dmz006/brain-drain/hardware/review/erc-summary.md

# ERC summary

kicad-cli 9 `sch erc`.

## brain

* 0 ERC findings (0 errors)

## card

* 2 ERC findings (0 errors)
  * warning: lib_symbol_mismatch: Symbol '2N7002' doesn't match copy in library 'Transistor_FET' (Symbol Q3 [2N7002])
  * warning: lib_symbol_mismatch: Symbol '2N7002' doesn't match copy in library 'Transistor_FET' (Symbol Q4 [2N7002])
