dmz006/brain-drain/hardware/review/routing-stats.md

# Routing statistics

Generated by `hardware/tools/make_review_pack.py`.

## brain

* 167 footprints, 192 nets, 3422 track segments, 568 vias
* copper length by layer (mm): B.Cu 466, F.Cu 1244, In2.Cu 4567, In3.Cu 5079
* vias (diameter / drill): 0.3/0.15 x 53, 0.45/0.2 x 480, 0.6/0.3 x 35
* differential-pair copper by layer (mm): B.Cu 202, F.Cu 372, In2.Cu 2250, In3.Cu 1812

**Reference planes of the pairs (review item):** pairs on In2 have the solid GND plane In1 next to them. Pairs on In3 have In4 next to them, which is split into power islands. Sampled every 0.5 mm along the In3 pair copper:

| plane under the pair (In4) | samples |
|---|---|
| +3V3 | 1315 |
| 5V_SYS | 1189 |
| +12V | 761 |
| 5V_HDD | 670 |

* 38 island-to-island transitions inside single segments, on 19 pair nets (each is a return-path discontinuity; stitching capacitors or a re-assigned In4 are the fixes).
* 833 of 3935 In3 pair samples (21 %) have an In2 track within 0.3 mm in plan view: broadside coupling between the two adjacent inner signal layers.

* 44 differential pairs, end-to-end skew (across the series capacitors) max 0.00 mm, table in `routing/pairs.md`

## card

* 39 footprints, 37 nets, 676 track segments, 133 vias
* copper length by layer (mm): B.Cu 742, F.Cu 694
* vias (diameter / drill): 0.3/0.15 x 31, 0.45/0.2 x 81, 0.6/0.3 x 21
* differential-pair copper by layer (mm): B.Cu 352, F.Cu 272

* 8 differential pairs, end-to-end skew (across the series capacitors) max 0.09 mm, table in `bay-card/routing/pairs.md`
