dmz006/brain-drain/docs/DECISIONS.md

# Decisions log

Open items block layout or software structure. Closed items record what was
chosen and why, so nobody re-litigates them later.

## Open

| # | Decision | Options | Recommendation | Blocks |
|---|---|---|---|---|
| D5 | OLED | 0.96"/1.3" 4-pin I2C vs 2.42" SSD1309 | 0.96"/1.3" for v1 | enclosure |
| D8 (applied 2026-09-23, pipeline rerunning) | Small vias for the QFN supply pins | 0.3 mm via / 0.15 mm drill for the dog-bones on the ASM1153E and USB5744 pins (0.4 mm pitch), staggered in two rows; JLCPCB lists 0.15 mm holes as standard on 4-layer boards (check the day's price list); everything else stays at 0.45/0.2 | recommended next lever: the 35 bridge-rail links and most of the 53 plane pins are exactly these pins; cheap to try, one pipeline rerun (about 5 h) | routing |
| D7 | Finishing the board | **(b) chosen 2026-09-23** ("try b, size can increase some if it helps"): board v3 at 150 × 112 mm, 2.5 mm around every QFN, hubs under the CM5's USB 3 pins, M.2 front-right; pipeline rerun: 81 % -> 83 %, pairs 9 -> 21 routed. Alternatives kept: (a) a board designer finishes the rest in the KiCad GUI; (c) finer fab rules (0.1 / 0.1 mm, 0.3/0.15 vias), now narrowed to D8 | owner's call | routing |
| D9 (decided: C24) | Bay cards and an 8-port brain | (1) stay monolithic, 4 bays; (2) brain + eight identical bay cards on PCIe-x1-style card-edge slots along the rear (bridge, switch, LED and receptacle per card; all 4 downstream ports of each hub used); (3) bridge at the drive end over USB-C (rejected: needs USB PD per port); (4) hub+bridges mezzanine (no gain) | (2) if 8 ports matter: the hard routing leaves the brain, the card routes in minutes and is built 8 times; box grows to ~155 × 120 × 55 mm, brick to 150–180 W, 8 drives at once share two 5 Gb/s uplinks. Brief: `decisions/2026-09-23-bay-cards.md` | architecture |
| D6 | Option B: bridges move into the cables | board = CM5 + hubs + 4× USB-A + switched 12 V/5 V outputs, about 90 × 70 mm; commercial USB 3 to SATA cables | parked by the owner on 2026-09-23 as a later study; A (C21) is being built | nothing now |
| D8 | Build order | software-sim first / schematic first / enclosure first | software-sim first (ARCHITECTURE §8) | everything |

## Closed

| # | Decision | Chosen | Why | Date |
|---|---|---|---|---|
| C1 | Drive pigtail | Off-the-shelf 22-pin SATA M-F extension; board has backplane-style 22-pin receptacles | no custom cable, drive end is native | 2026-09-21 |
| C2 | Staggered spin-up | Mandatory, per-bay P-FET switches on 12 V and 5 V from GPIO | halves peak input current; also gives unfreeze/reset | 2026-09-21 |
| C3 | Two 5 V bucks | separate 5V_SYS and 5V_HDD, same TPS56637 | keep spin-up ripple off the CM5 rail | 2026-09-21 |
| C4 | RTC on board | PCF85063AT + CR2032 | certificates need timestamps off-network | 2026-09-21 |
| C5 | Default wipe policy | HDD: 1-pass zeros + full verify (Clear). SSD: Sanitize crypto-scramble then block-erase (Purge). Multi-pass only as explicit legacy modes | NIST 800-88 Rev. 2 | 2026-09-21 |
| C6 | Enclosure tool | OpenSCAD with params generated from KiCad | ubiquitous, easy to diff | 2026-09-21 |
| C7 (was D9) | Compute module | **CM5** | $10 over CM4 at equal RAM/eMMC; 2× native USB 3.0 so four HDDs run at native speed; PCIe Gen3 x1 left free; on-module RTC | 2026-09-22 |
| C8 (was D1, D4) | USB 3 topology | CM5 USB 3.0 port → VL817 hub → 2× ASM1153E, twice. No PCIe xHCI | ~400 MB/s per pair of bays, no firmware loading, uses the originally requested VL817 | 2026-09-22 |
| C9 (was D6) | Module size | CM5002016 (2 GB, 16 GB eMMC) for production; CM5002000 Lite via microSD for dev | service needs < 1 GB; eMMC can't fall out mid-job; same carrier serves both | 2026-09-22 |
| C10 | User interaction | No Start button. A drive is wiped as soon as it is detected (after a 5 s grace countdown); unplugging aborts; DIP is the only control | single-purpose appliance, keep it simple | 2026-09-22 |
| C11 | USB 3.0 hub | **Microchip USB5744**, one per CM5 USB 3.0 port | same 4-port 5 Gbit/s spec as VL817; fully public datasheet; smallest and cheapest; JLCPCB-assembled; +1 LDO for 1.2 V core | 2026-09-23 |
| C12 (was D3) | USB→SATA bridge | **ASMedia ASM1153E** | dmz's call: Linux track record (UASP+TRIM, no quirks) over the public-datasheet rule; datasheet from a mirror copy, kept locally in hardware/ref/datasheets (not committed) | 2026-09-23 |
| C13 (was D2) | 12 V input | **4-pin DIN Kycon KPJX-4S-S only**; barrel footprint dropped | barrels are 5 A rated, design peak is 7.4 A; DIN is 7.5 A/pin and what 12 V/10 A bricks ship with. Brick must be chosen before layout to match DIN pin assignment | 2026-09-23 |
| C14 (was D7) | Panel LEDs | **3 mm through-hole**, 6 off | cheapest, tolerant of enclosure error, bay LEDs blink with real disk activity | 2026-09-23 |
| C15 (was D10) | M.2 NVMe bay | **Populated in v1**: M.2 M-key on PCIe Gen3 x1, switched 3V3, enclosure access door | dmz's call: NVMe wipes from day one; accepts door + PCIe rescan software as v1 work | 2026-09-23 |
| C16 | Schematic workflow | **Generated**: `hardware/tools/design.py` is the source of truth; `gen_sch.py` regenerates the KiCad sheets and `gen_connections.py` the connection list on every change; placement is tidied in the GUI only once the netlist settles | ERC on every edit, repeated bay sheets cannot drift, connection list always in sync | 2026-09-23 |
| C17 | SATA bay receptacle | **Molex 47018-4001**, right-angle SMT 22-pin host receptacle | industry standard, precise sales drawing SD-47018-001, easy small-quantity sourcing | 2026-09-23 |
| C18 | M.2 socket | **TE 2199230-4**, 4.2 mm M-key | most common small-run M.2 socket, stocked at distributors and JLCPCB | 2026-09-23 |
| C19 | Board outline | **Option A: 180 × 110 mm**, all cables on the rear edge (DIN, RJ45, USB-C/UART, 4× SATA), CM5 centred, M.2 along the front with its door on a side wall | one enclosure wall with cutouts, single cable exit, M.2 door away from cables, fits a 220 mm print bed | 2026-09-23 |
| C20 | Licence | **Polyform Noncommercial 1.0.0** for hardware, software and enclosure | matches the owner's datawatch project; source-available, noncommercial | 2026-09-23 |
| C22 | Wireless instead of Ethernet | **Option A**: CM5 wireless variant, unit runs a Wi-Fi access point with an ephemeral 8-character key regenerated at every boot and shown on the OLED as text and as a Wi-Fi QR code; a phone page (stdlib HTTP) shows status, certificates (download one or all), the log, and lets the owner push a network to join (remembered, joined at boot) or reset. Wi-Fi reset / factory reset from the page (with the key), from DIP mode 110 at boot (110 + DIP 8 = factory), or `braindrain wifi-reset`. RJ45 magjack removed. CM5 antenna edge on the left board edge, 8 mm copper-free strip, no metal within 10 mm | standalone appliance; the owner asked for ESPHome-style ephemeral provisioning, liked the QR code, and wants certificates reachable from a phone | 2026-09-23 |
| C23 | No buzzer, passive cooling, lid opens for the M.2 | Buzzer, its FET and diode removed (GPIO18 free). Passive CM5 cooler by default, fan header kept. The M.2 socket sits flat on the board and the lid hinges open (rear hinge, front snap latch, lid microswitch = the bay-5 "door") instead of a wall slot | fewer parts, the phone page and LEDs carry the signal; I/O-bound workload; simpler and tighter case | 2026-09-23 |
| C24 | Brain + bay cards, eight slots, four populated (D9 option 2, variant A) | **Brain** 150 × 122 mm: CM5 on the right edge (antenna out), two USB5744 hubs with all four downstream ports used, eight PCI Express x1 sockets along the rear edge (bay-card pinout, 14.5 mm pitch), M.2 bay 9, DIN / USB-C / microSD on the left wall. **Bay card** 40 × 46 mm, one design: ASM1153E, switched 12 V / 5 V with PTC fuses, 22-pin SATA receptacle on its top edge, PCIe-x1 fingers; the cable rises through a lid window. v1 populates slots 1-4; slots 5-8 take cards later (brick 150-180 W). Bay LEDs stay on the brain, sunk by the card through the edge | owner: "lets go with A" after the cost table; the hard routing leaves the brain, one card routes in minutes, expansion is plug-in | 2026-09-23 |
| C25 | Bay-card switch FET: AOS AON7403 (P-channel, −30 V, DFN 3×3-8) | fully public datasheet, stocked at JLCPCB, standard power pin-out | owner: "go with your recommendation" | 2026-09-23 |
| C26 | Brain board goes to six layers (F sig, In1 GND, In2 sig, In3 sig, In4 power, B sig); the bay card stays four | the last ten connections were boxed in by copper on both outer layers; six layers add roughly $70–130 to a first run of two assembled and three bare boards | owner: "Go ahead with the sixth layer" | 2026-09-24 |
| C28 | Each hub's ten bypass capacitors sit on the bottom side of the brain | on the top they competed with the hubs' pin escapes and via fanout; on the bottom they have their own layer; adds a little double-sided assembly | design (routing analysis 2026-09-24) | 2026-09-24 |
| C29 | Pair length matching is measured end to end across the series coupling capacitors | the link is one channel from the transmitter to the receiver; the segments beyond the caps can carry the compensation; a reviewer may still want the mismatch removed where it arises (LAYOUT-REVIEW 4.1) | design | 2026-09-25 |
| C30 | Bay cards are held by a comb under the lid and grooved blocks under the rear overhang; the lid and the boards carry the logo, name and repository URL | the lid did not touch the cards, which stand 49 mm tall and overhang the board by 15 mm; ribs 2.6 mm wide between the receptacle housings (0.4 mm clearance both sides, plug path free) and eight blocks with a 2.0 mm groove under the card shoulders stop rocking. The octopus logo is engraved 0.6 mm into the lid and drawn as silkscreen on the brain board (with the URL), the name on the card. Also fixes the lid features, which had been modelled front to back | owner: "add the comb and overhang support", "add ... the logo and name and on the board the same + the url" | 2026-09-25 |
| C31 | Input fuse F1 raised from 10 A to 15 A slow-blow (Littelfuse 0453015.MR, same NANO2 footprint) | eight bays need about 11.7 A at a staggered peak, above the 10 A fuse; the DIN jack is 7.5 A per pin with two pins per polarity, so 15 A is its limit. Q20 (12 A) and the 5V_HDD buck are not changed and are flagged for the review | owner: "change the input fuse to 15 A" | 2026-09-26 |
| C27 | Bay card widened to 45 mm; cards overhang the brain's rear edge (option A) | the Molex 47018-4001 receptacle is 40.46 mm wide (customer drawing SD-47018-001), so the 40 mm card cannot carry it; a centred 45 mm card would hide the bay LEDs, so the fingers sit 6 mm from the card's front edge and the card overhangs the rear edge of the board by about 15 mm; box 16 mm deeper (about 157 × 145 × 62 mm) | owner: "go with option A ... make it work" | 2026-09-25 |
| C21 | Portable "brain box" (supersedes C19) | **Option A**: bridges stay on the board, drives on 22-pin cables, no rack or chassis. Board **150 × 98 mm**: 4× SATA on the rear at 28.9 mm pitch, DIN / RJ45 / USB-C on the left wall, microSD + M.2 SSD slot on the front wall, CM5 landscape centre, hubs and bucks in the right column, M.2 vertical along the right edge, CR2032 and buzzer on the bottom. Enclosure about 157 × 105 × 39 mm | owner wants the unit, brick and cables in a backpack and drives loose on the bench; A keeps every chosen part (ASM1153E, per-bay power, allow-list, M.2) and only the outline and enclosure change. Option B (D6) parked for later. Brief: `decisions/2026-09-23-portable-brain.md` | 2026-09-23 |
