dmz006/brain-drain/docs/RENDERS.md

# Renders and drawings

Everything here is generated. Board and assembly views come from a proxy 3D model (`hardware/tools/board_model.py`: the outline extruded
to 1.6 mm plus a box for every part body, sized from the courtyards and a height table), so they show layout and fit, not exact
component shapes. The case is the real OpenSCAD geometry. Regenerate all of it with:

```
cd hardware && for p in brain card; do BD_PROJECT=$p sh tools/render_board.sh; done   # KiCad 3D views, per-layer images, schematic PNGs
cd ../enclosure && make && make renders                                              # STLs, then docs/img/renders/*.png
software/.venv/bin/python docs/tools/diagrams.py                                     # block diagram, lid plan, wall panel, bay flow
```

## Boards, one at a time

| Brain board, rear (slots) | Brain board, from above |
|---|---|
|  |  |

| Brain board, front left | Brain board, bottom side |
|---|---|
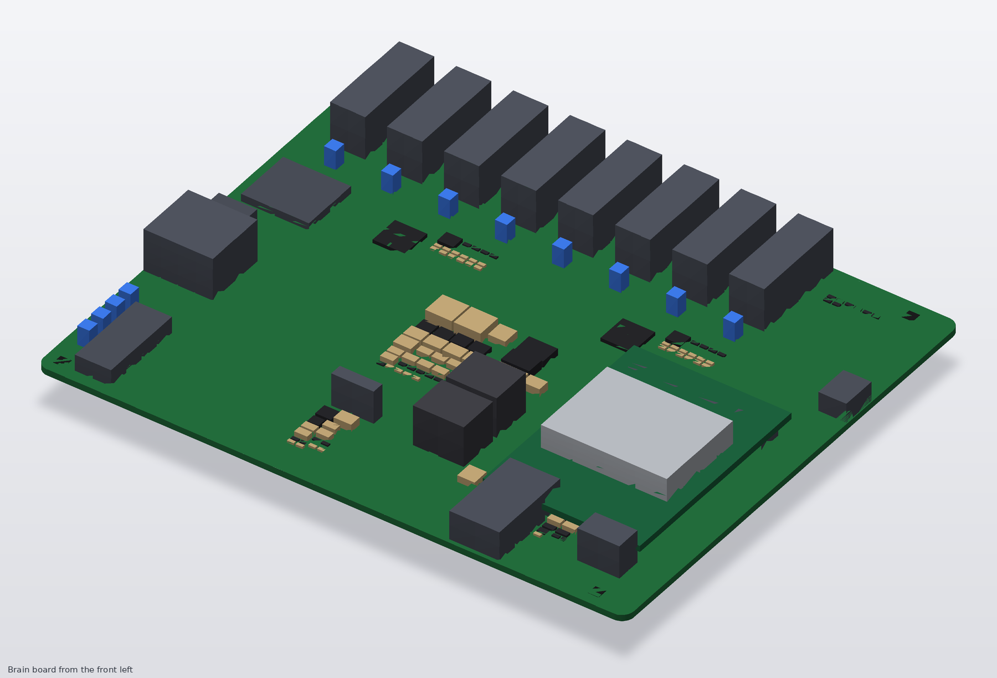
[picture p15: docs/img/renders/brain-iso-front.png]
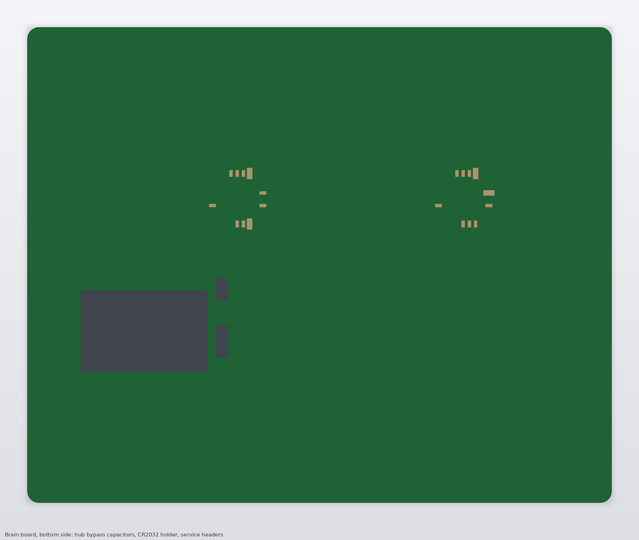
[picture p16: docs/img/renders/brain-bottom.png]
|  |  |

| Bay card, component side | Bay card, 3D | Bay card, back |
|---|---|---|
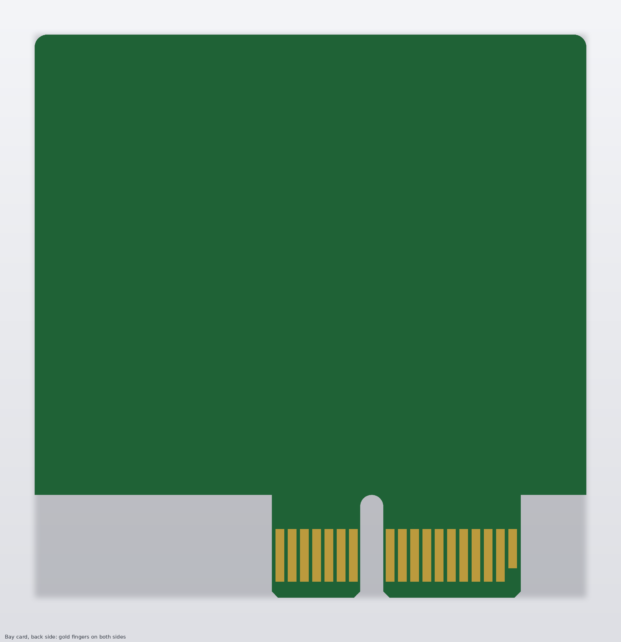
[picture p17: docs/img/renders/card-back.png]
|  |  |  |

KiCad's own 3D views (bare copper, no part bodies) and the layer images:

| Brain, KiCad 3D | Brain, F.Cu | Brain, In3.Cu |
|---|---|---|
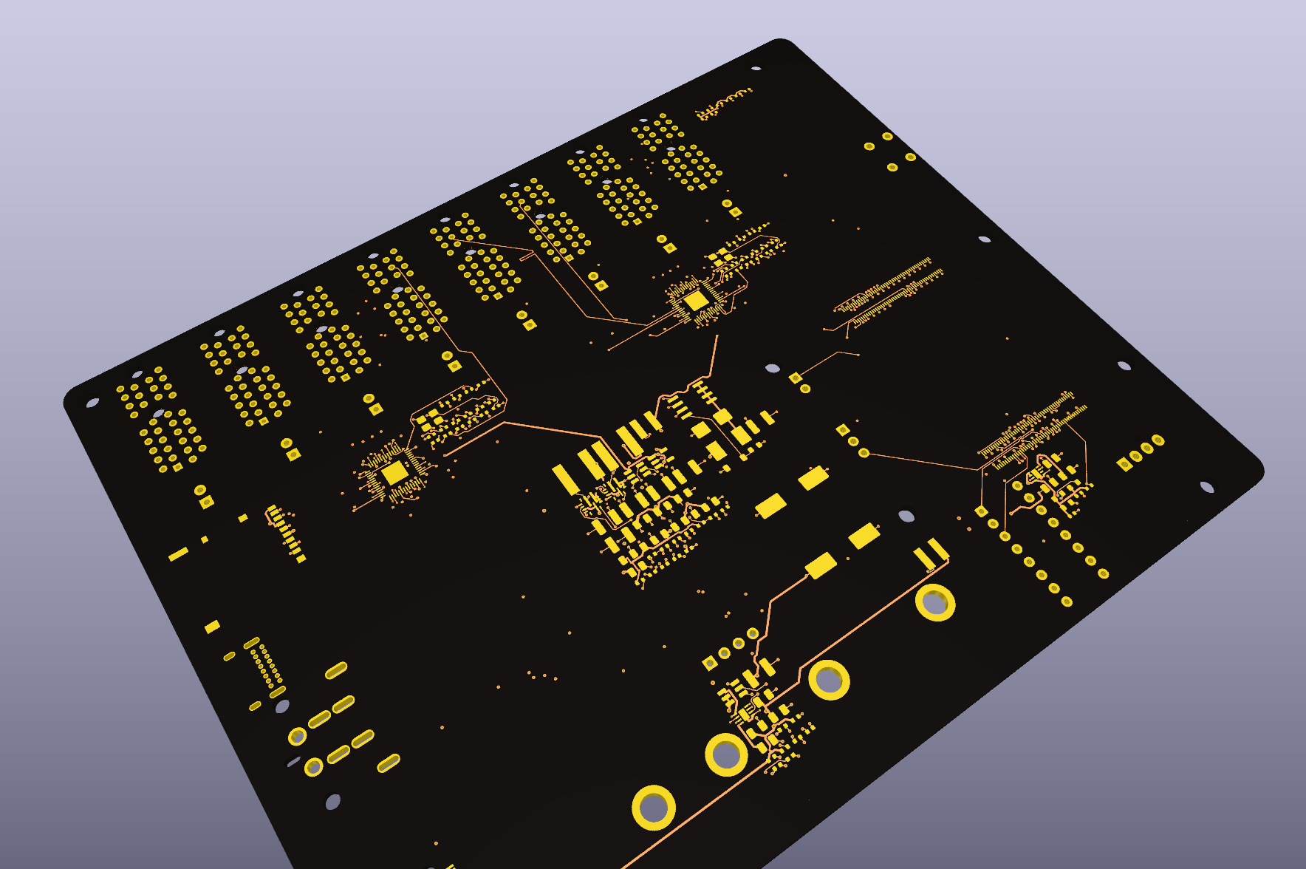
[picture p18: hardware/renders/board-3d-iso.png]
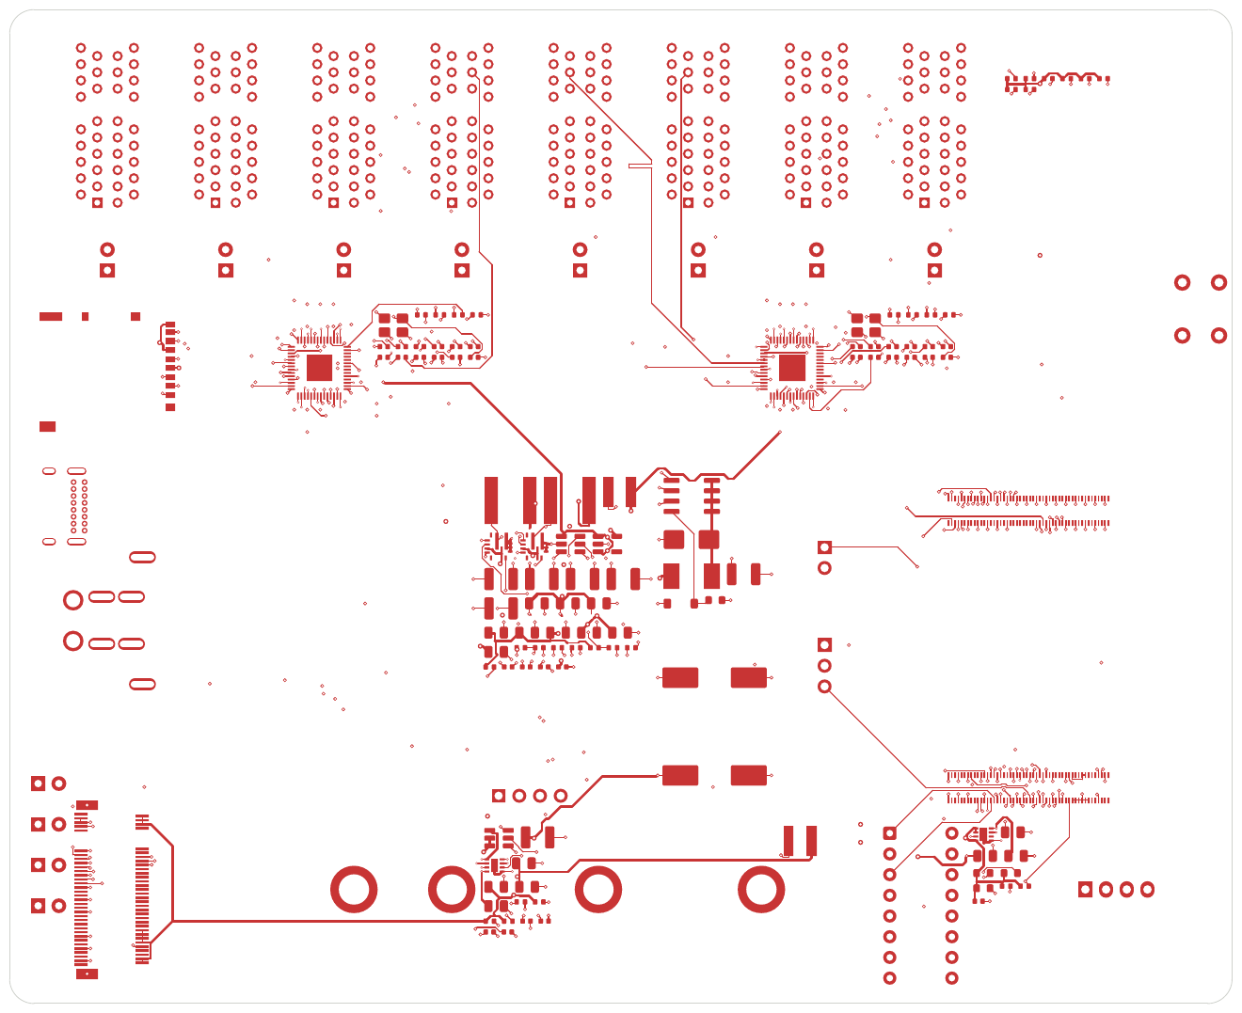
[picture p19: hardware/renders/layers/F.Cu.png]
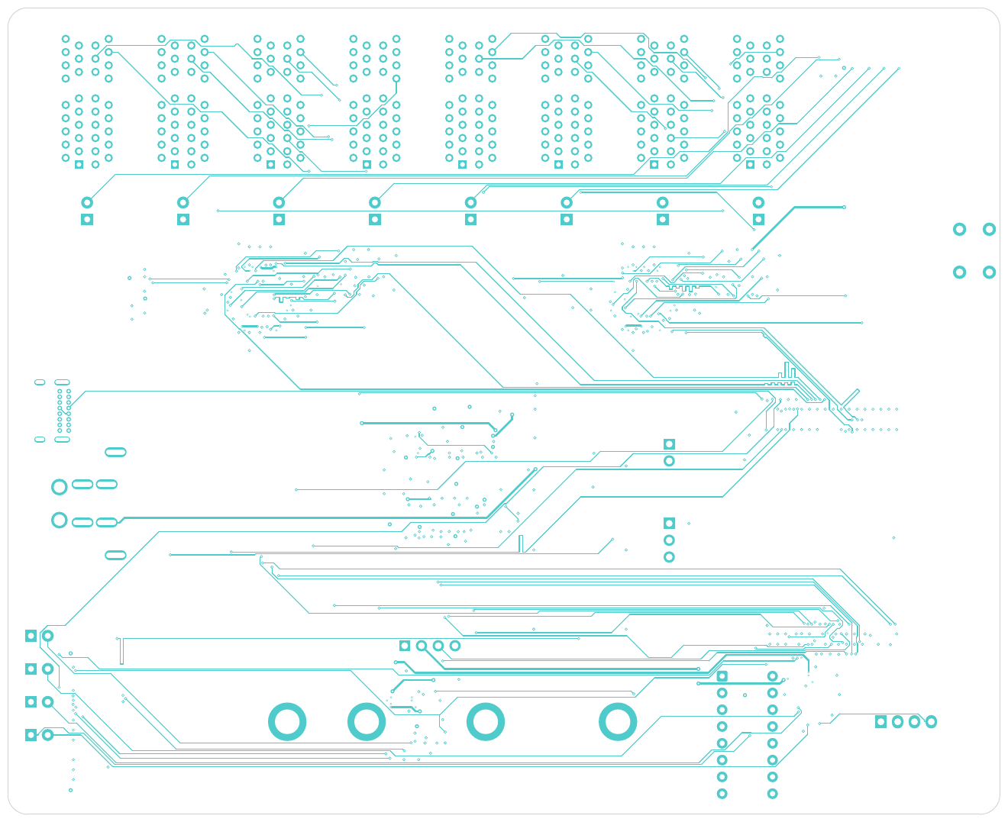
[picture p20: hardware/renders/layers/In3.Cu.png]
|  |  |  |

All layers: `hardware/renders/layers/` (F.Cu, In1 to In4, B.Cu, assembly-top, assembly-bottom, mask) and `hardware/bay-card/renders/layers/`;
schematic sheets: `hardware/renders/schematic/`; PDFs: `hardware/review/*-schematic.pdf`.

## The assembled electronics

| Brain with four bay cards, from the rear left | From the front left |
|---|---|
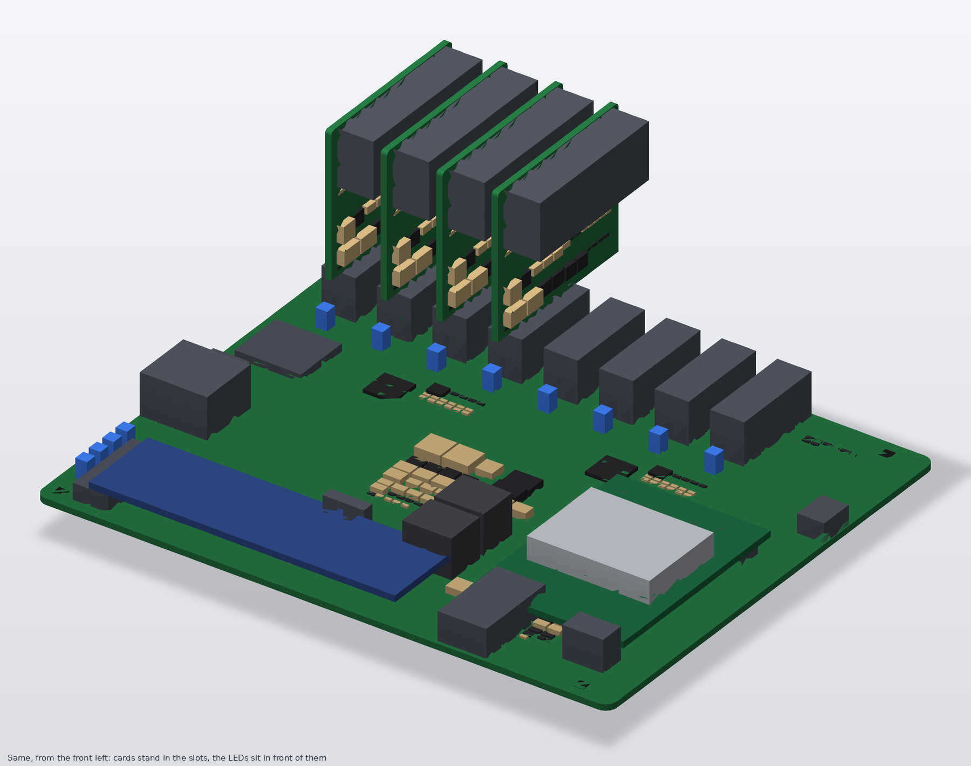
[picture p21: docs/img/renders/electronics-iso-front.png]
|  |  |

| Plan view (cards overhang the rear edge by 15 mm) | Side view (card top 48.9 mm above the board) |
|---|---|
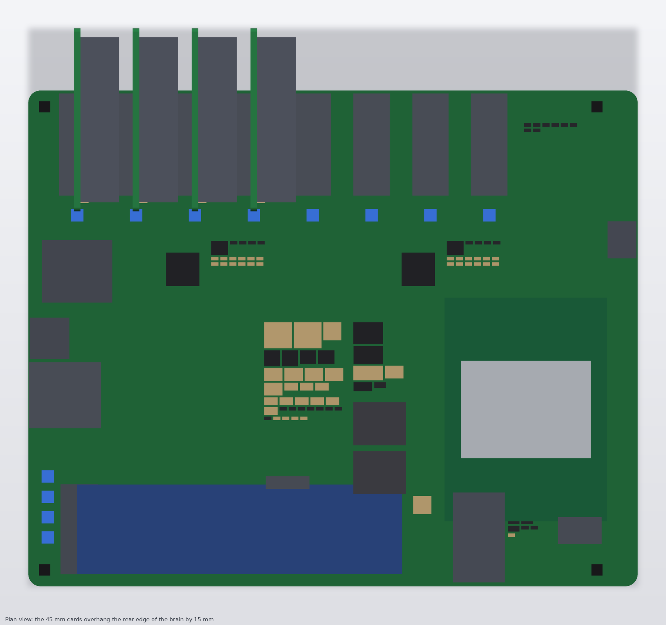
[picture p22: docs/img/renders/electronics-top.png]
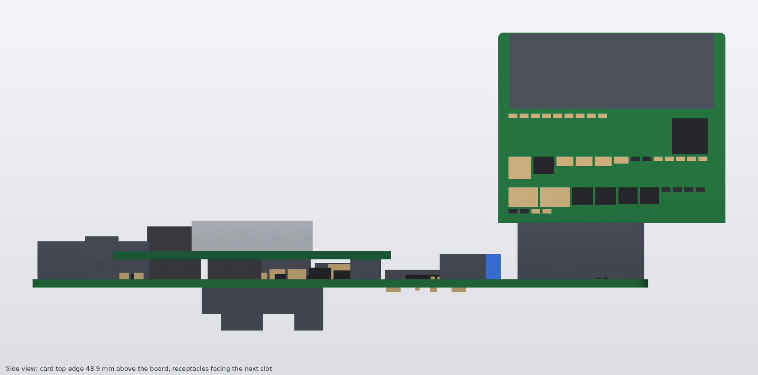
[picture p23: docs/img/renders/electronics-side.png]
|  |  |

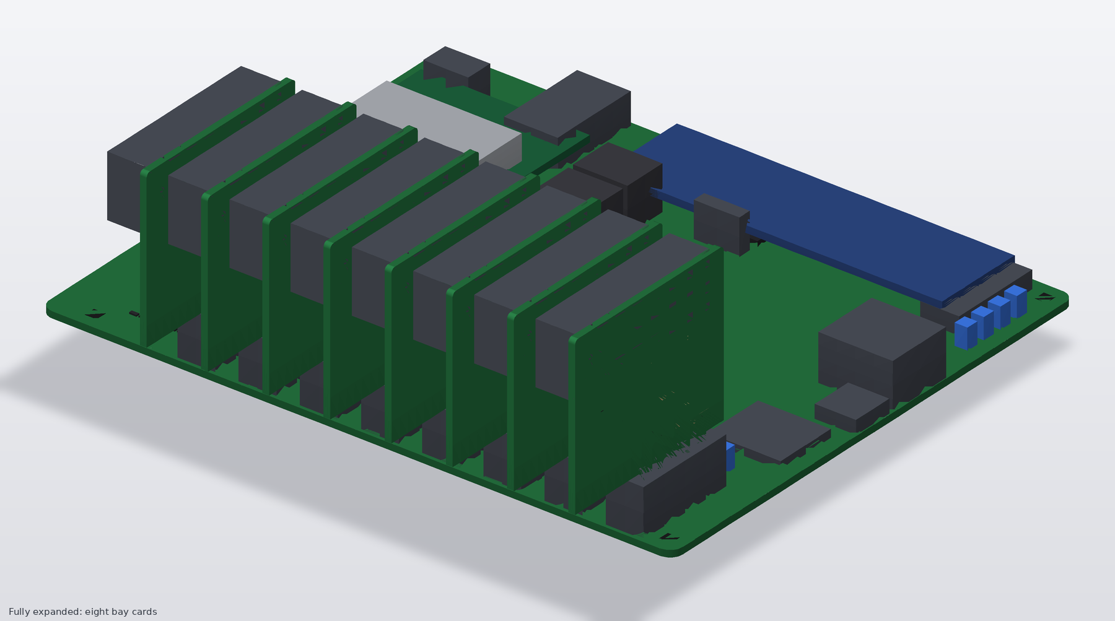
[picture p24: docs/img/renders/electronics-full8.png]
all eight slots populated


## The case

| Tray | Lid, outside |
|---|---|
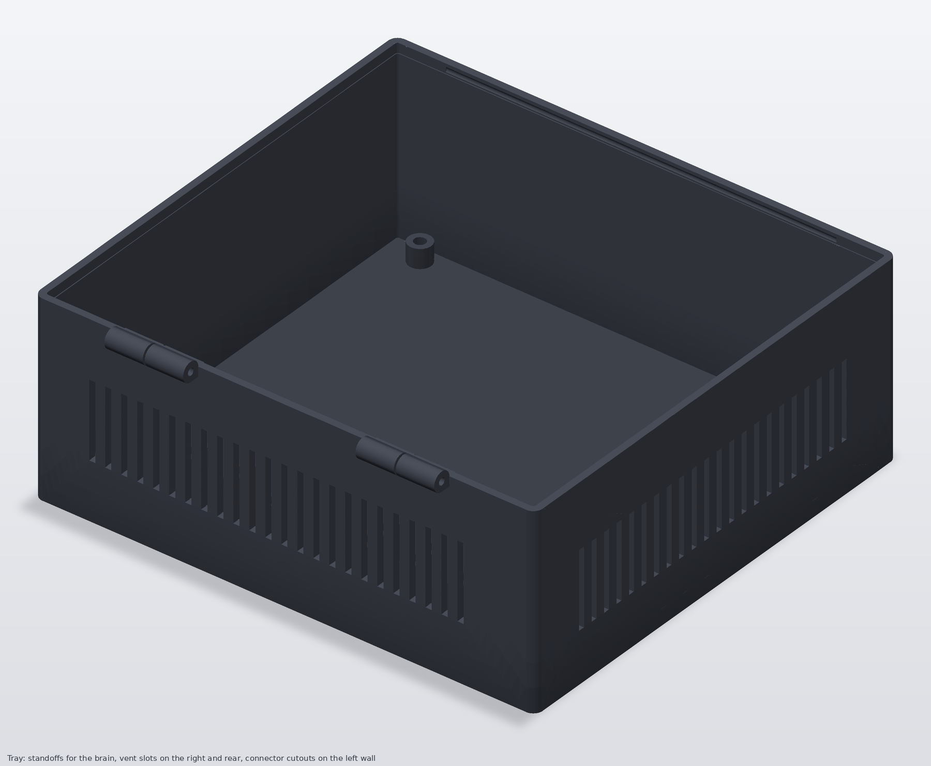
[picture p25: docs/img/renders/case-tray-iso.png]
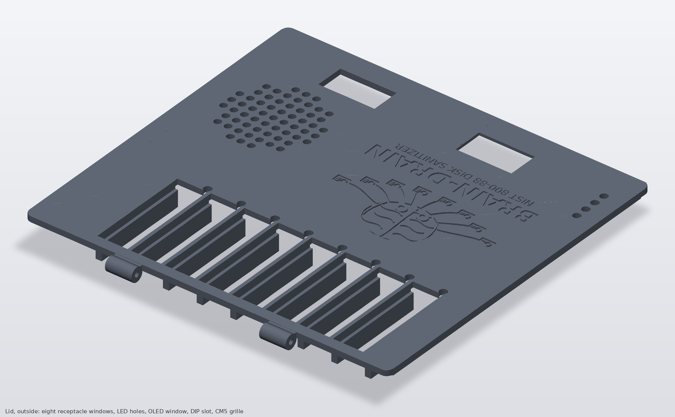
[picture p26: docs/img/renders/case-lid-outside.png]
|  |  |

| Lid, inside (printed face down) | Tray from above |
|---|---|
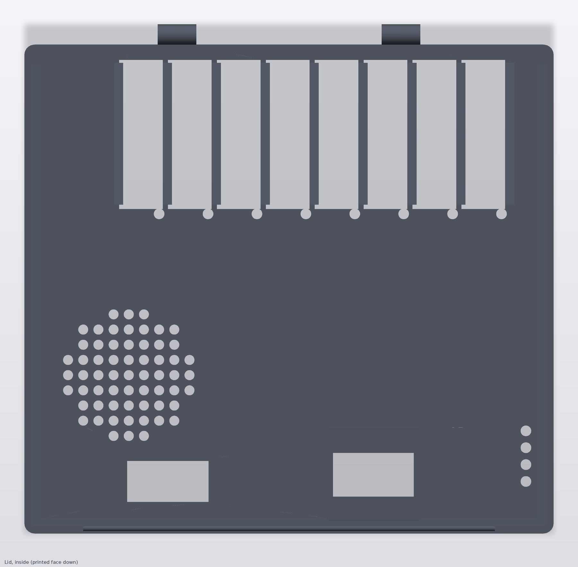
[picture p27: docs/img/renders/case-lid-inside.png]
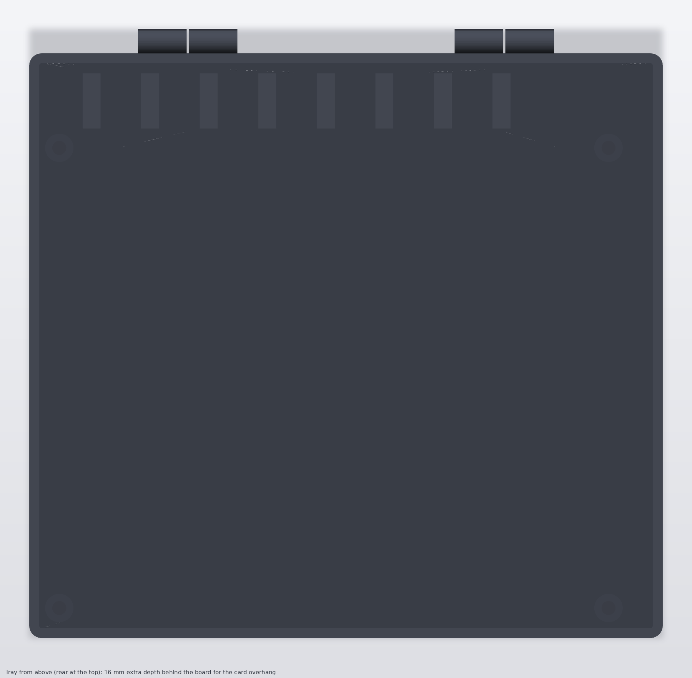
[picture p28: docs/img/renders/case-tray-top.png]
|  |  |

Lid artwork (engraved logo and name) and the comb ribs seen through the windows:

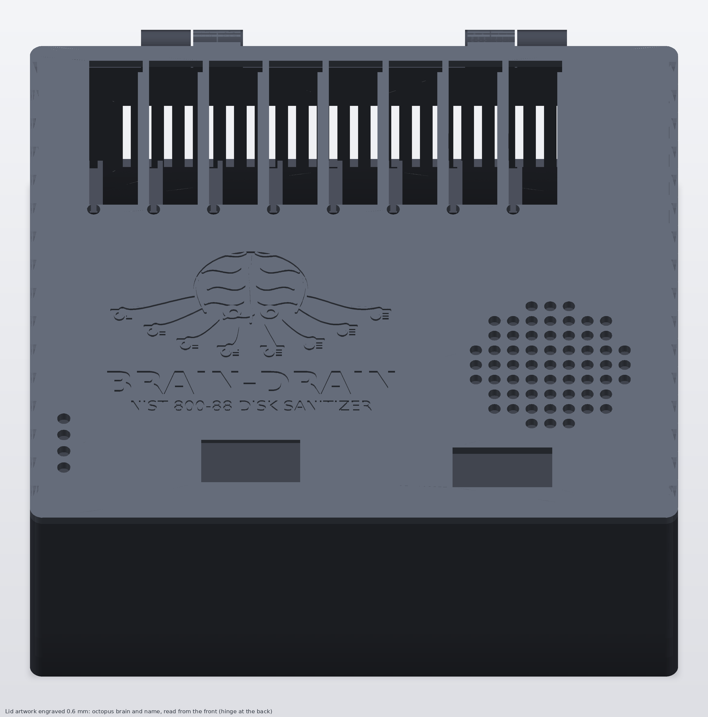
[picture p29: docs/img/renders/case-lid-artwork.png]


Brain board top silkscreen (logo, name, revision and repository URL are the `branding` group; the rest is reference text):

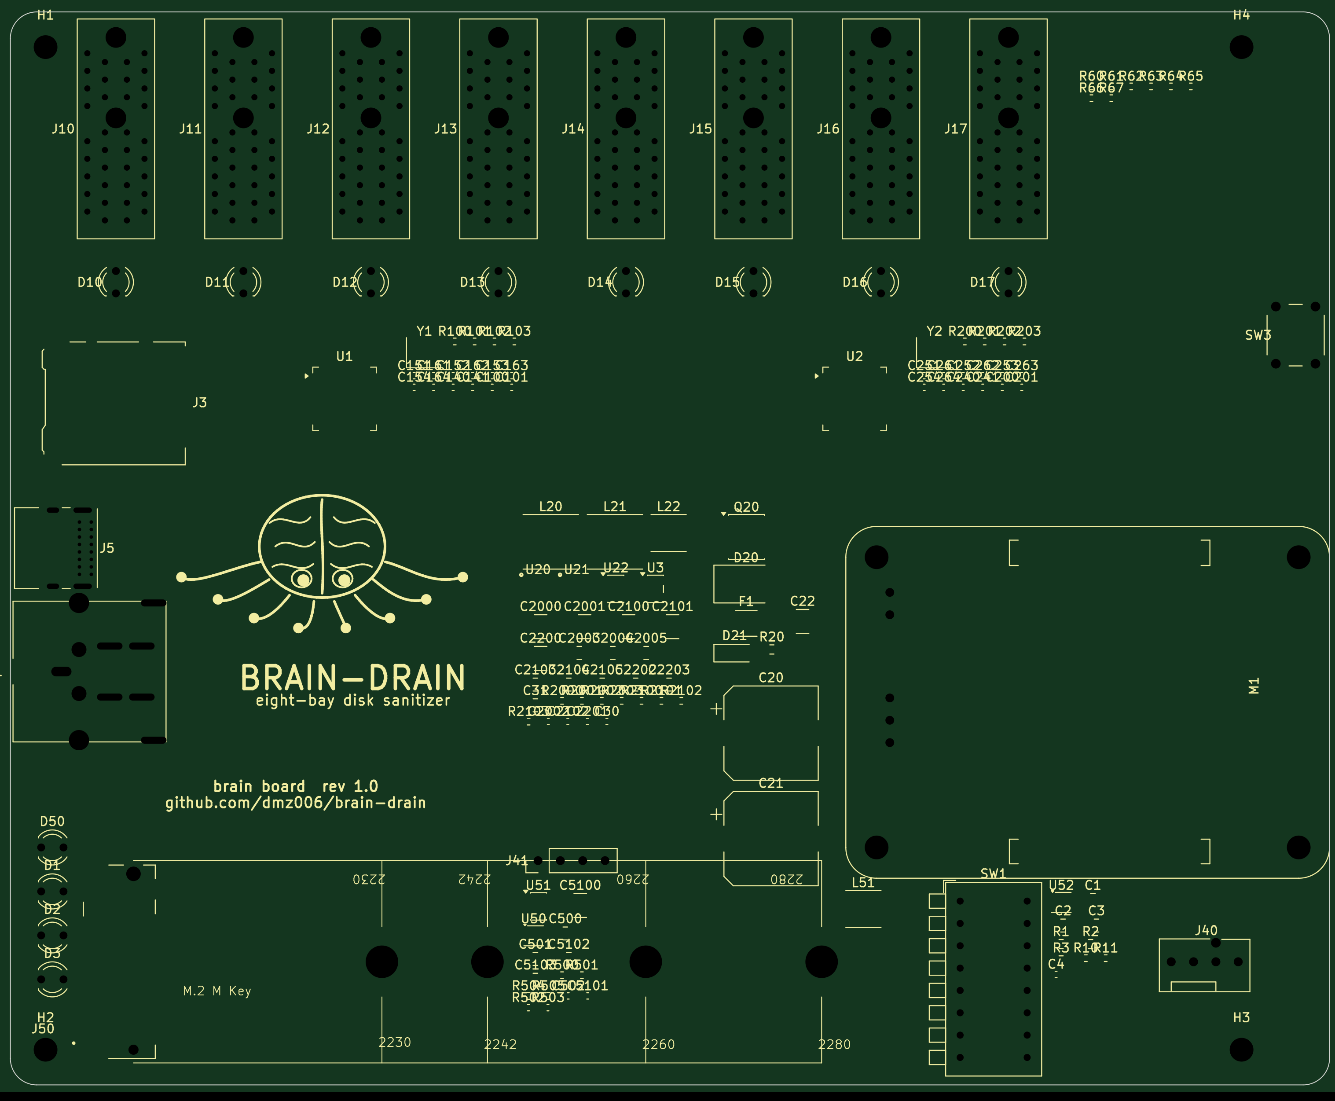
[picture p30: docs/img/renders/board-silk.png]


Logo close-up:

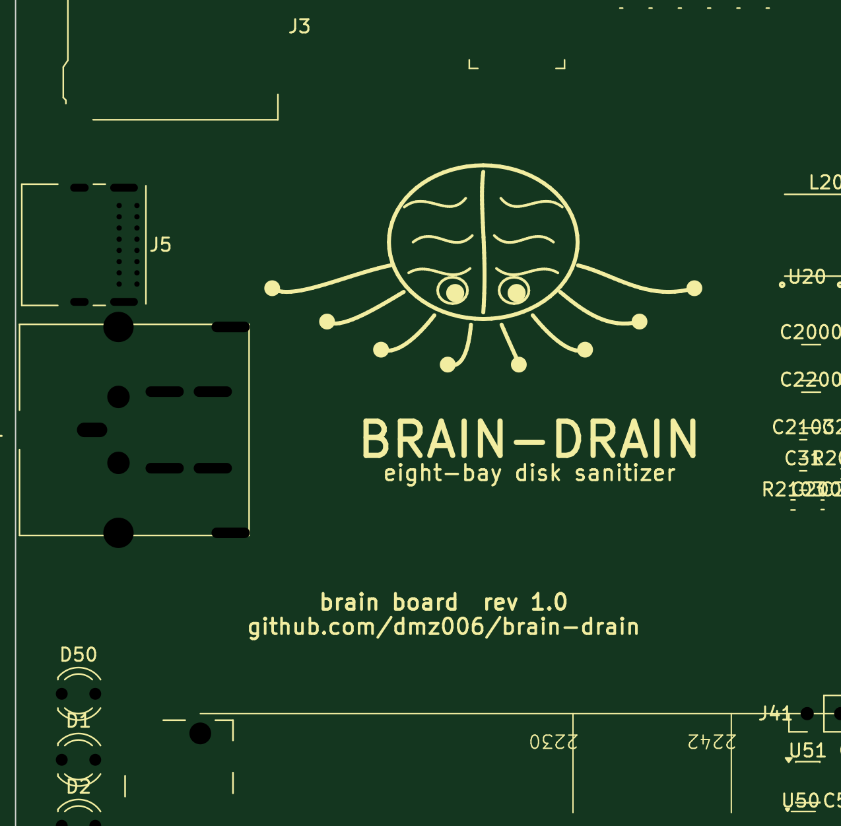
[picture p31: docs/img/renders/board-silk-logo.png]


| Closed, from the rear left | Closed, from the front right |
|---|---|
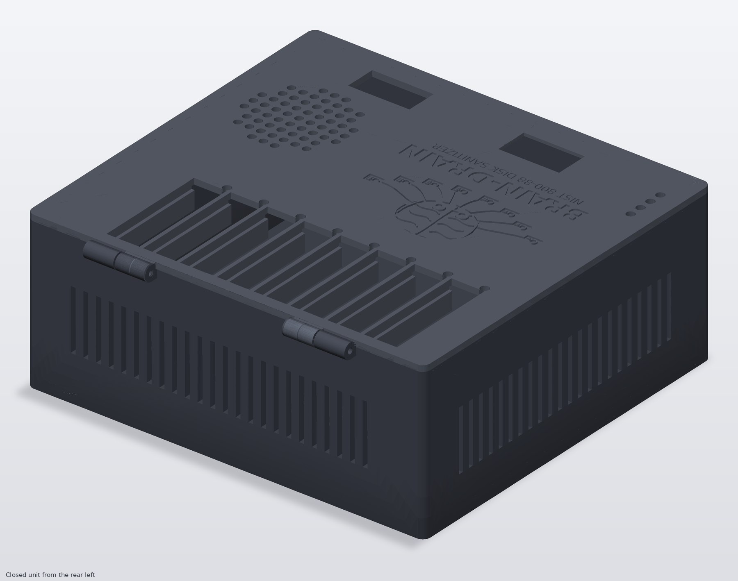
[picture p32: docs/img/renders/case-closed-iso.png]
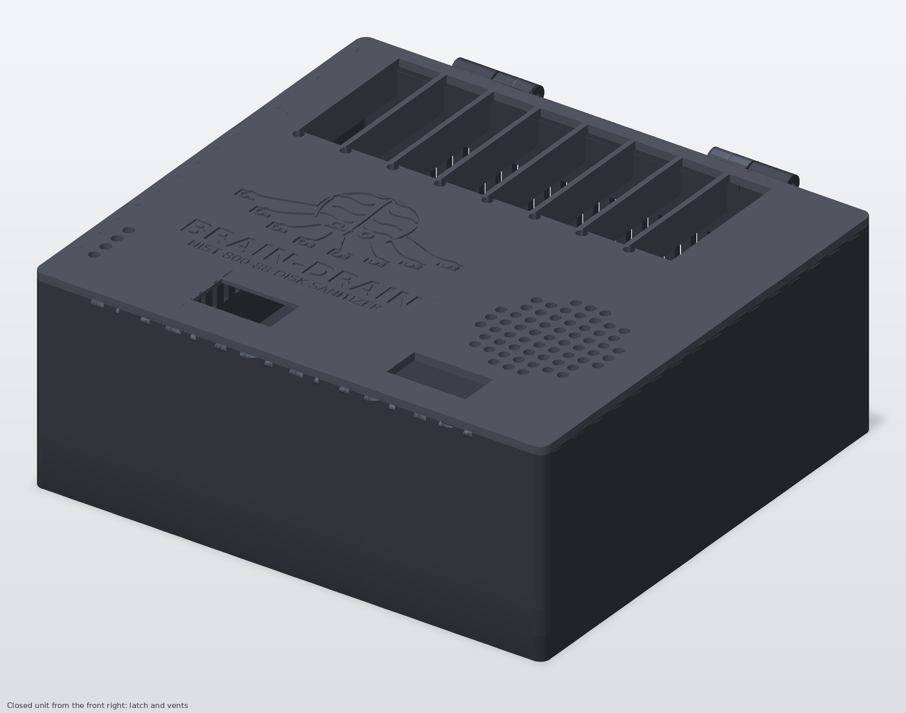
[picture p33: docs/img/renders/case-closed-front.png]
|  |  |

Plan drawing with dimensions, windows and holes: lid plan

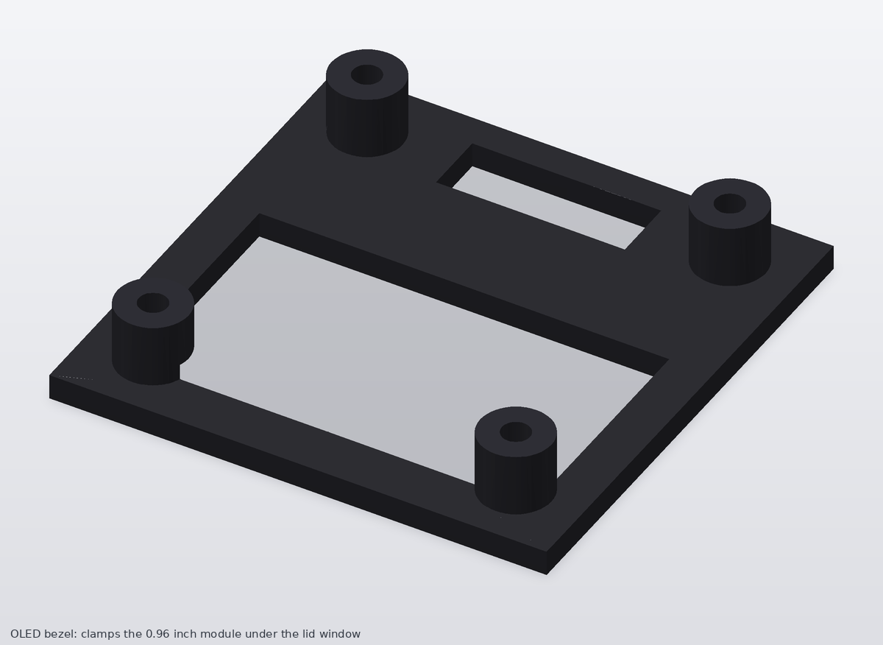
[picture p34: docs/img/renders/case-bezel.png]
OLED bezel: 

## The unit with the electronics inside

| Lid open, from the front | Lid removed |
|---|---|
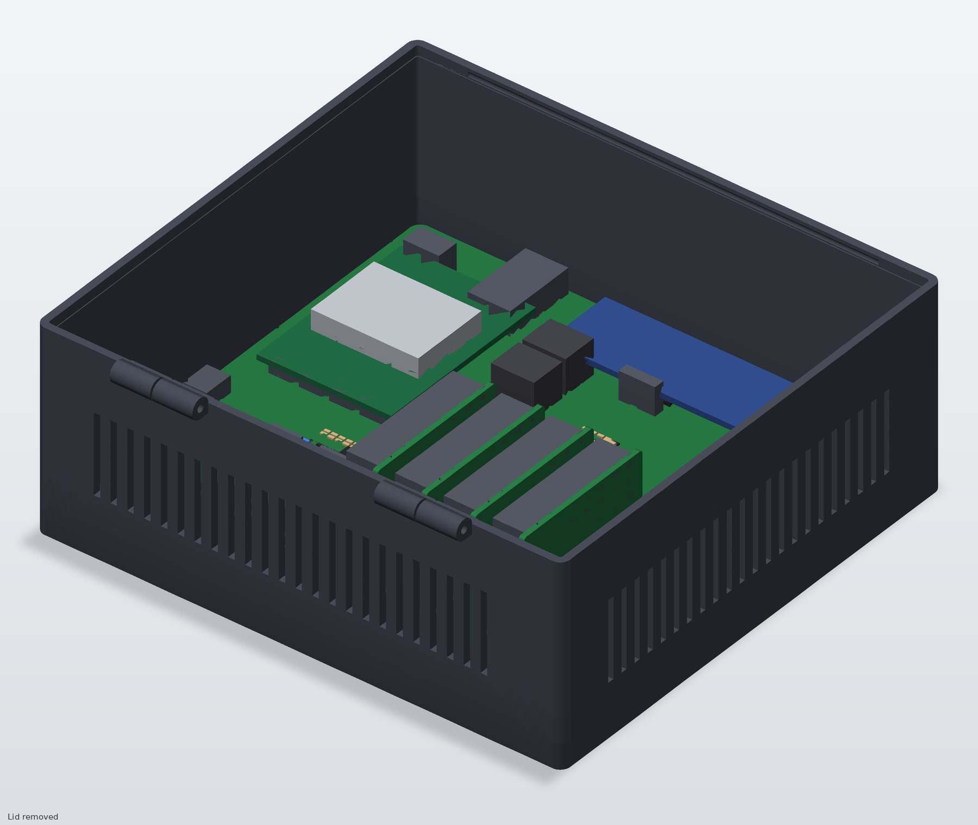
[picture p35: docs/img/renders/unit-no-lid.png]
|  |  |

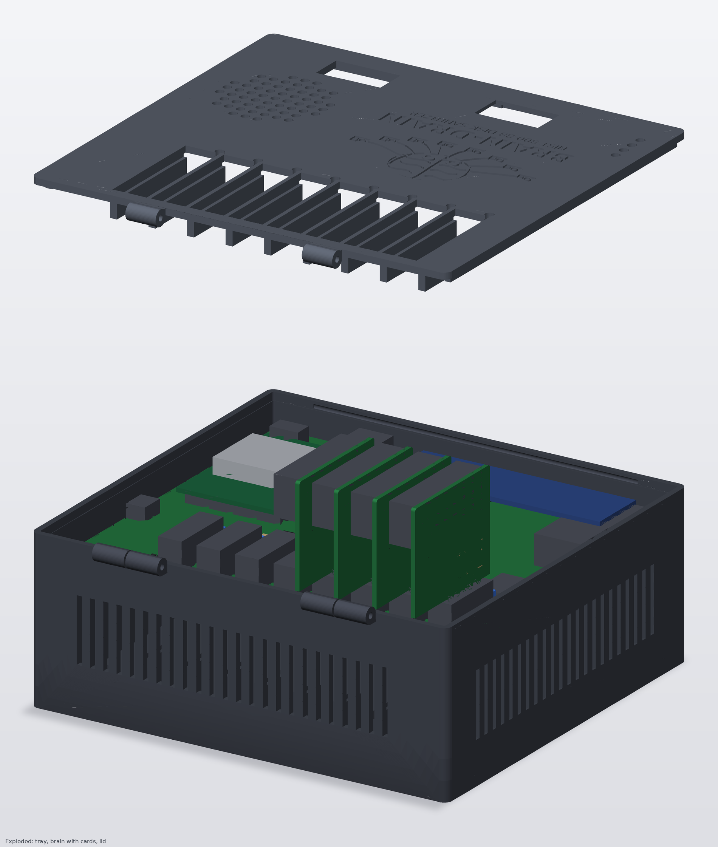
[picture p36: docs/img/renders/unit-exploded.png]
exploded


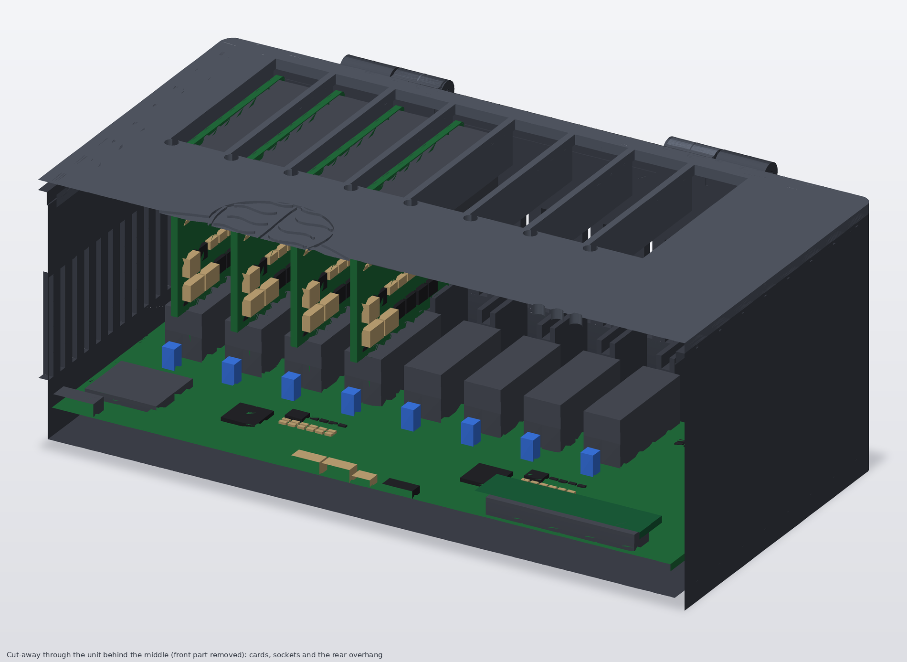
[picture p37: docs/img/renders/unit-cutaway.png]
cut-away


## The complete system

The unit, four drives on 0.5 m 22-pin cables rising through the lid windows, and the 12 V brick on the DIN cable.



| From above | From the front right |
|---|---|
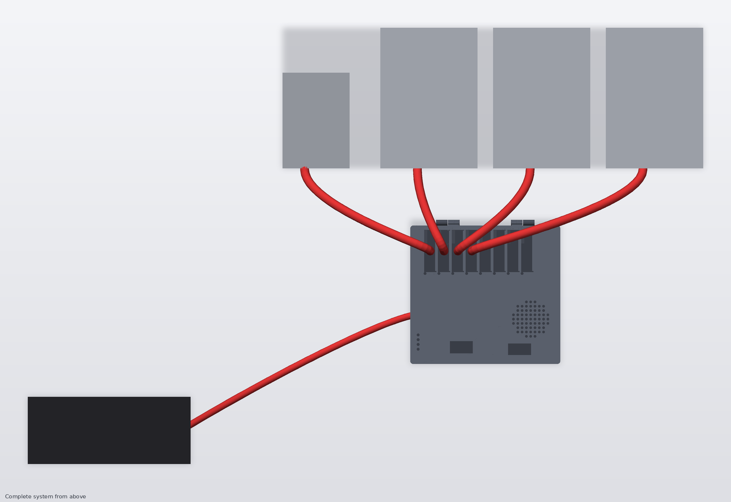
[picture p38: docs/img/renders/system-top.png]
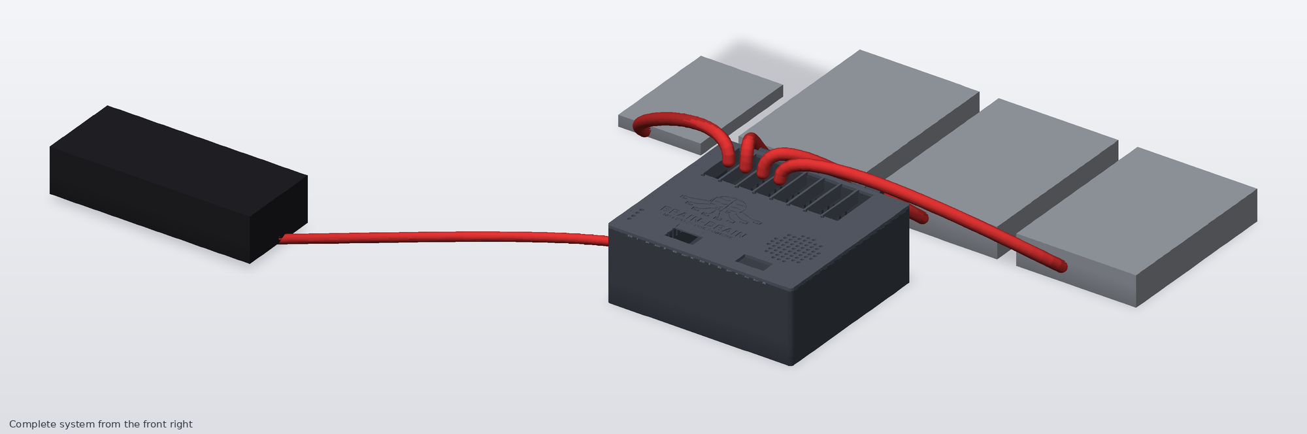
[picture p39: docs/img/renders/system-front.png]
|  |  |

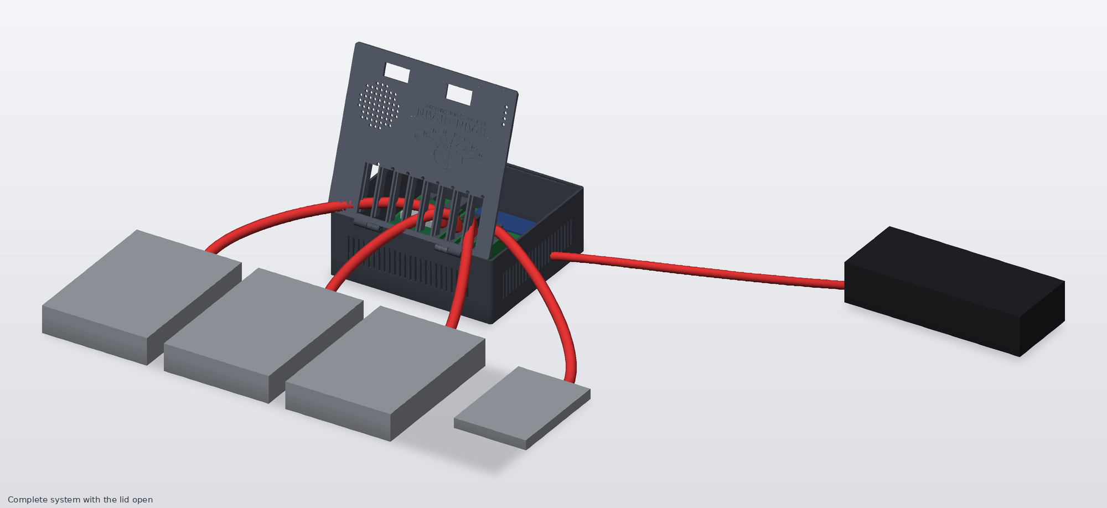
[picture p40: docs/img/renders/system-open.png]
lid open


## Diagrams

| | |
|---|---|
| system | bay flow |
| left panel | oled |
