dmz006/brain-drain/docs/img/oled-errors.png

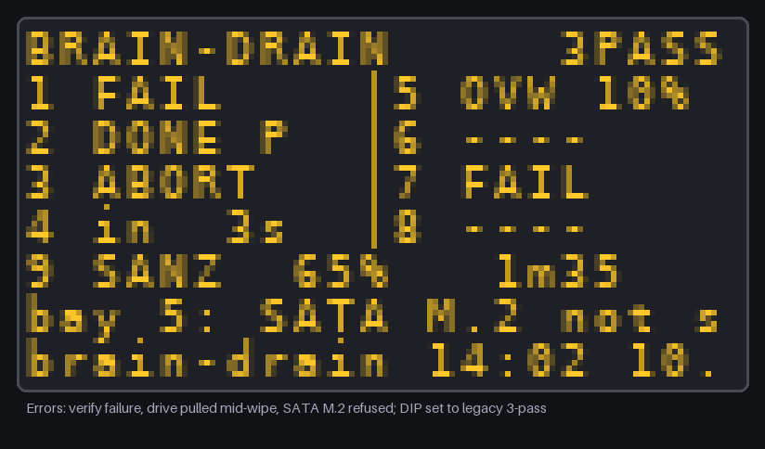
docs/img/oled-errors.png
