dmz006/brain-drain/docs/img/oled-idle.png

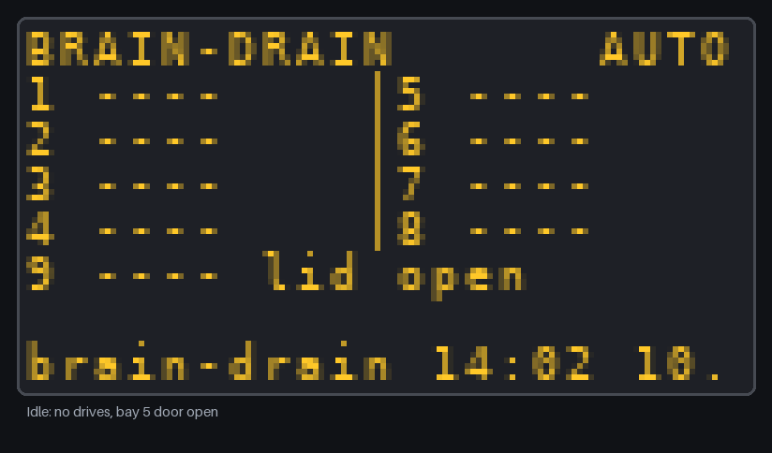
docs/img/oled-idle.png
