dmz006/brain-drain/docs/img/renders/case-closed-top.png

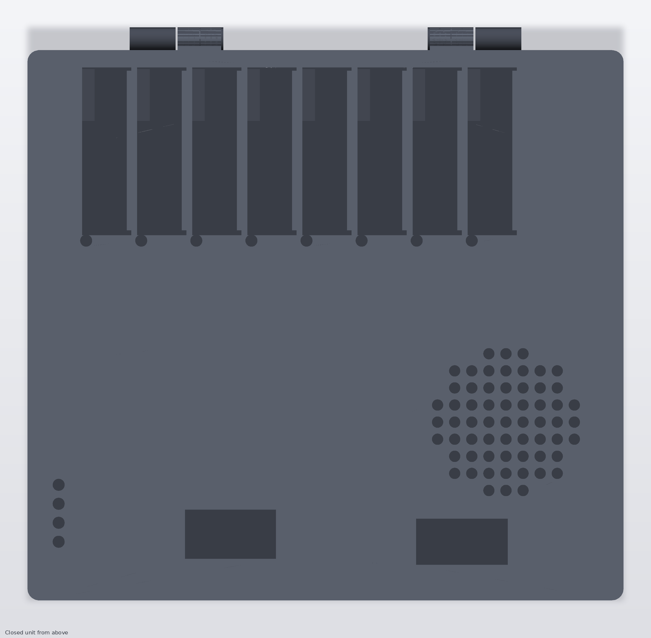
docs/img/renders/case-closed-top.png
