dmz006/brain-drain/docs/img/renders/unit-open.png

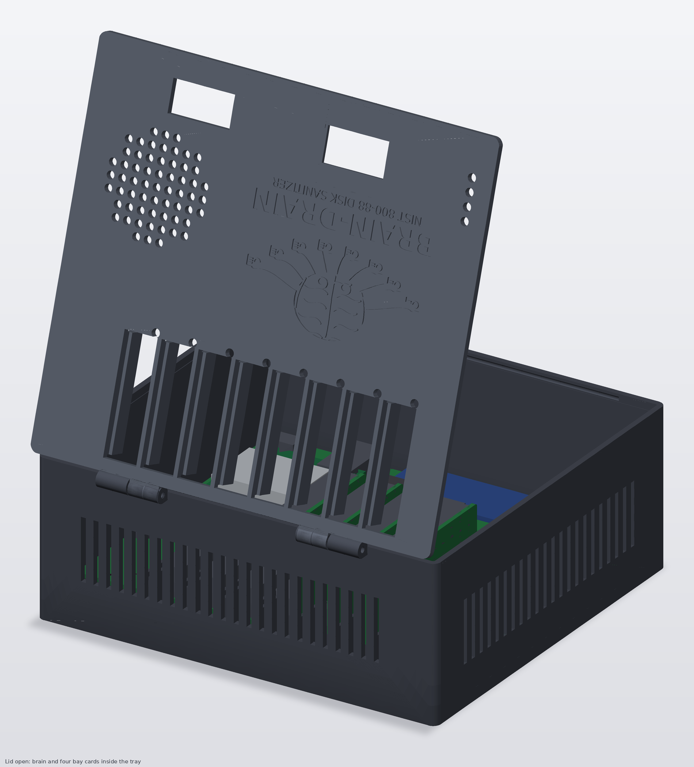
docs/img/renders/unit-open.png
