dmz006/brain-drain/hardware/bay-card/renders/board-3d-bottom.png

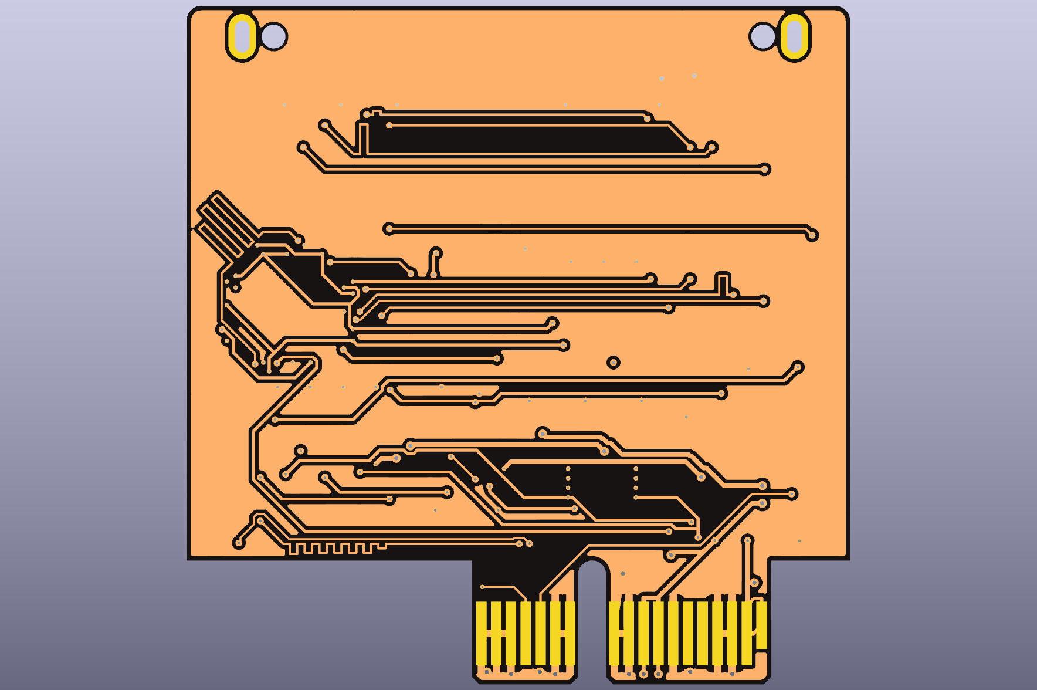
hardware/bay-card/renders/board-3d-bottom.png
