dmz006/brain-drain/hardware/bay-card/renders/board-3d-top.png

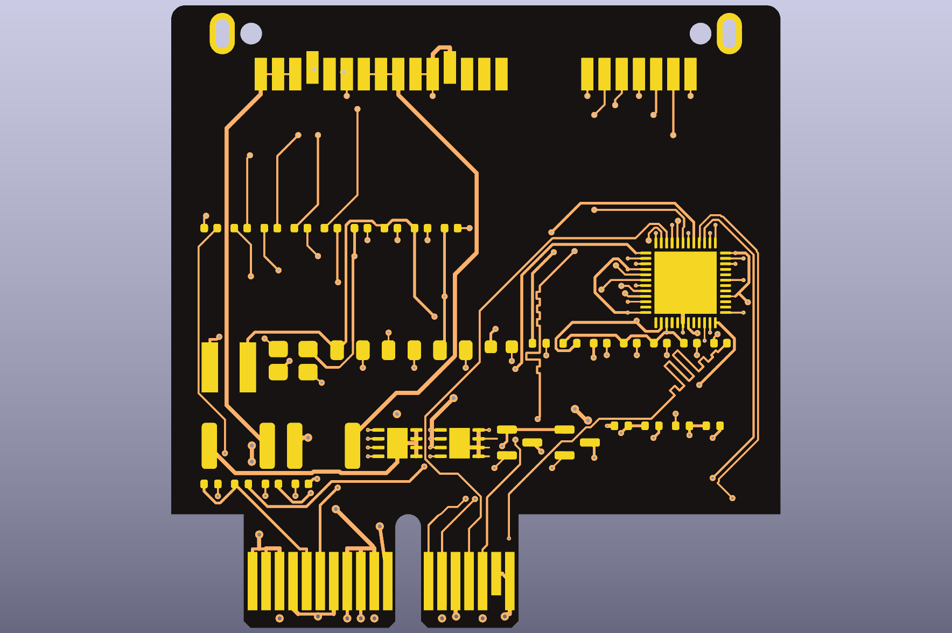
hardware/bay-card/renders/board-3d-top.png
