dmz006/brain-drain/hardware/bay-card/renders/board-top.png

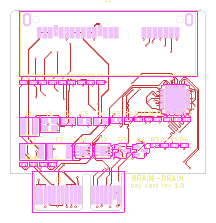
hardware/bay-card/renders/board-top.png
