dmz006/brain-drain/hardware/bay-card/renders/layers/B.Cu.png

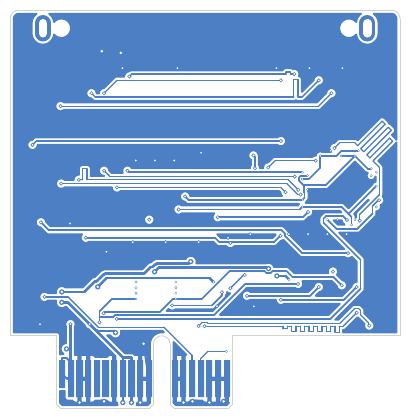
hardware/bay-card/renders/layers/B.Cu.png
