dmz006/brain-drain/hardware/bay-card/renders/layers/F.Cu.png

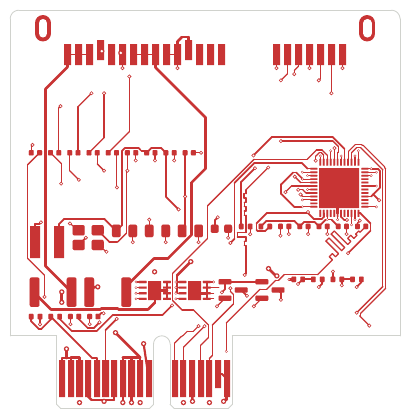
hardware/bay-card/renders/layers/F.Cu.png
