dmz006/brain-drain/hardware/bay-card/renders/layers/In1.Cu.png

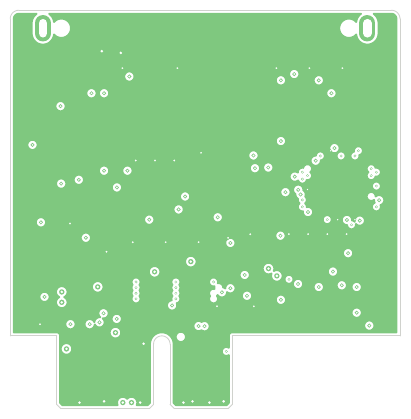
hardware/bay-card/renders/layers/In1.Cu.png
