dmz006/brain-drain/hardware/bay-card/renders/layers/mask.png

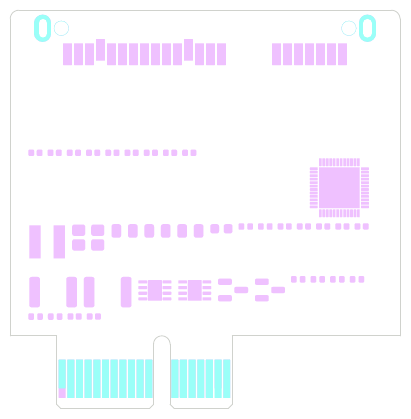
hardware/bay-card/renders/layers/mask.png
