dmz006/brain-drain/hardware/bay-card/renders/schematic/sheet-3.png

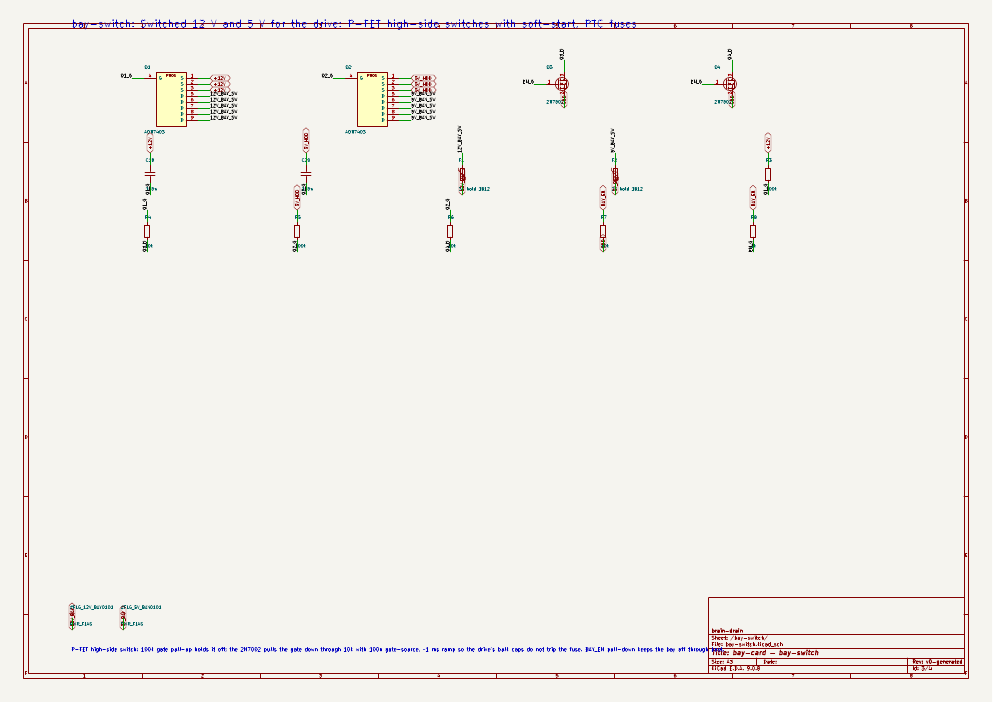
hardware/bay-card/renders/schematic/sheet-3.png
