dmz006/brain-drain/hardware/bay-card/renders/schematic/sheet-4.png

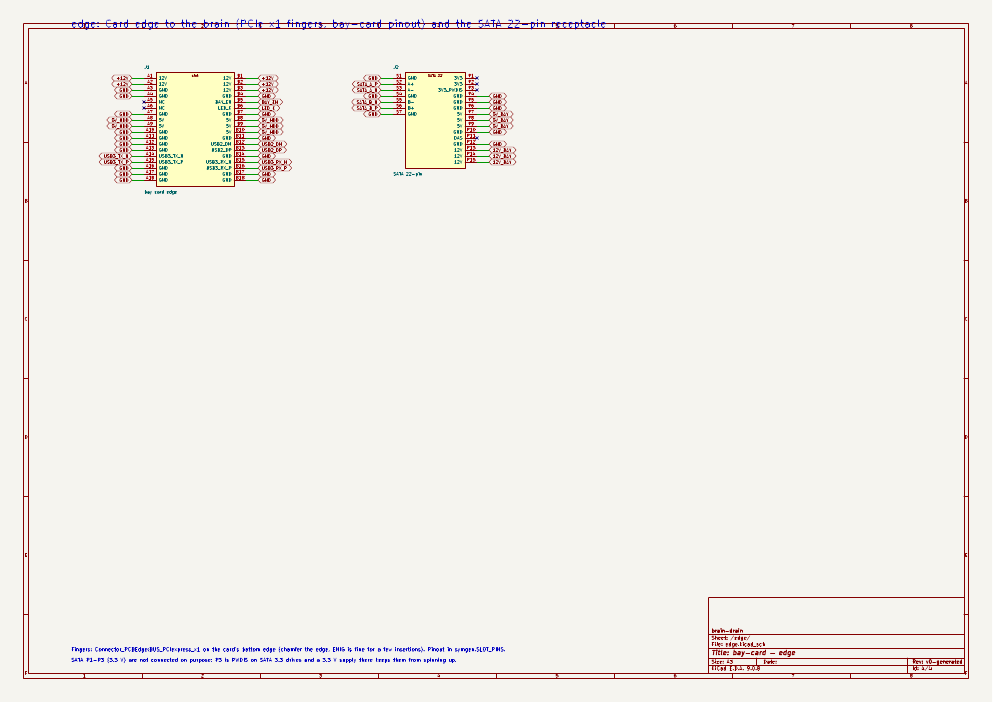
hardware/bay-card/renders/schematic/sheet-4.png
