dmz006/brain-drain/hardware/renders/board-3d-bottom.png

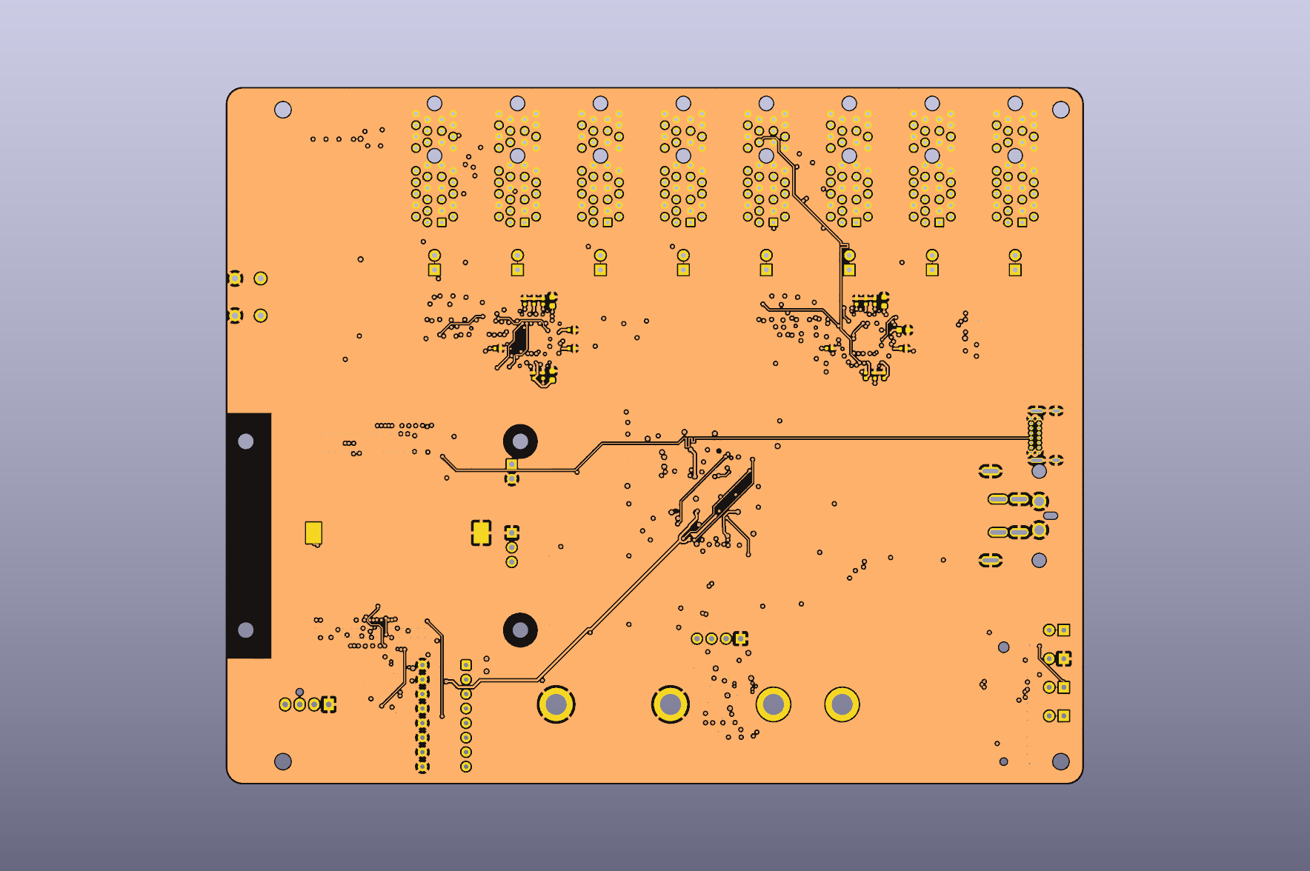
hardware/renders/board-3d-bottom.png
