dmz006/brain-drain/hardware/renders/board-3d-top.png

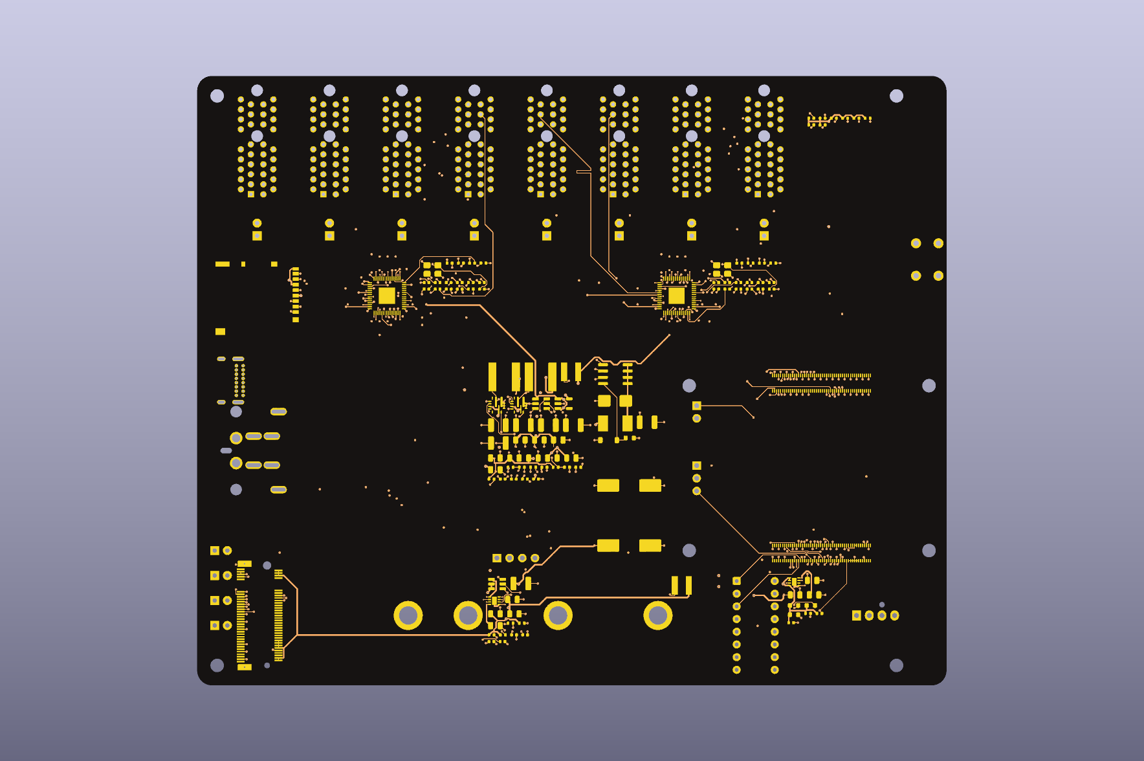
hardware/renders/board-3d-top.png
