dmz006/brain-drain/hardware/renders/board-inner.png

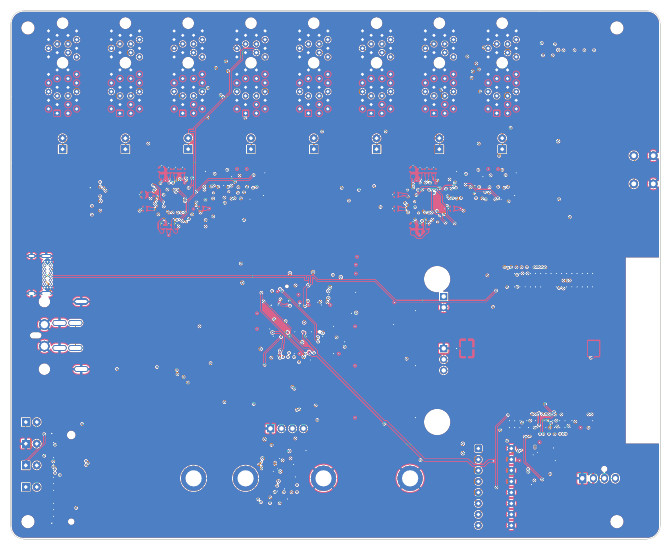
hardware/renders/board-inner.png
