dmz006/brain-drain/hardware/renders/board-top.png

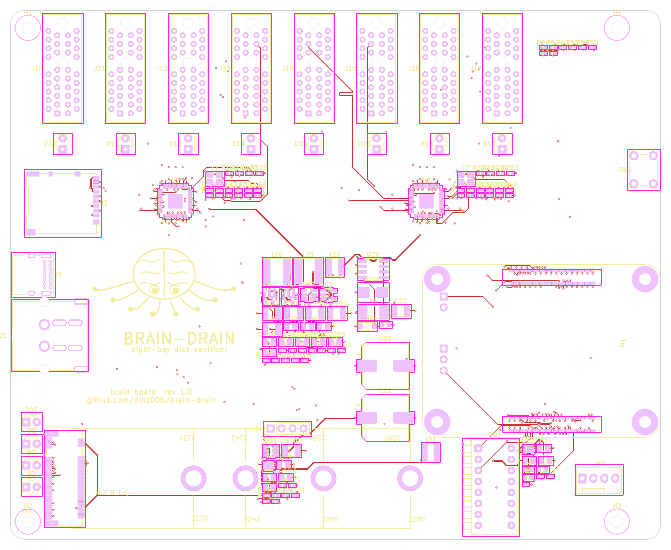
hardware/renders/board-top.png
