dmz006/brain-drain/hardware/renders/layers/B.Cu.png

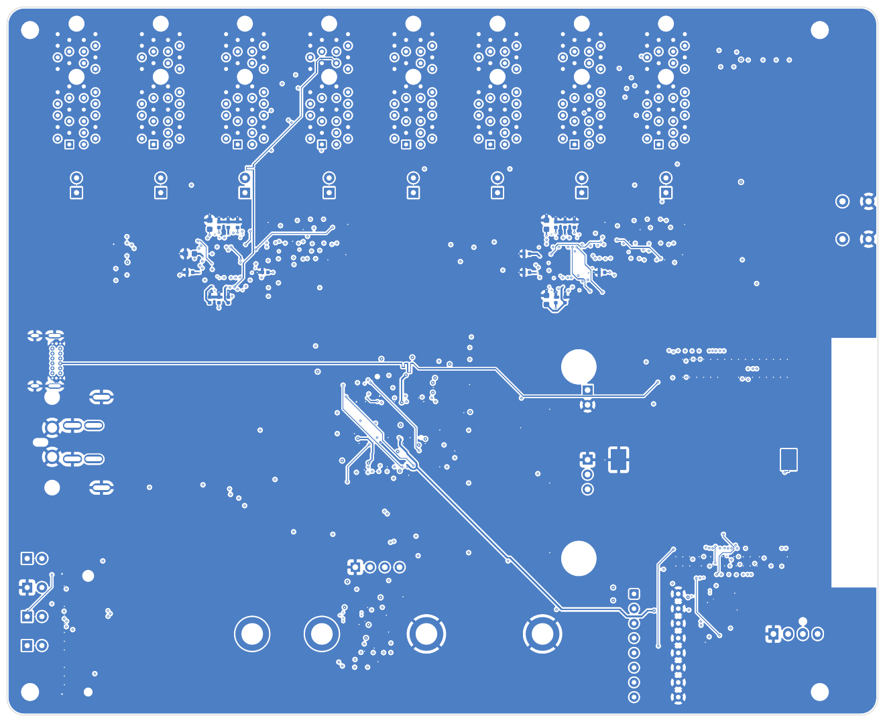
hardware/renders/layers/B.Cu.png
