dmz006/brain-drain/hardware/renders/layers/In2.Cu.png

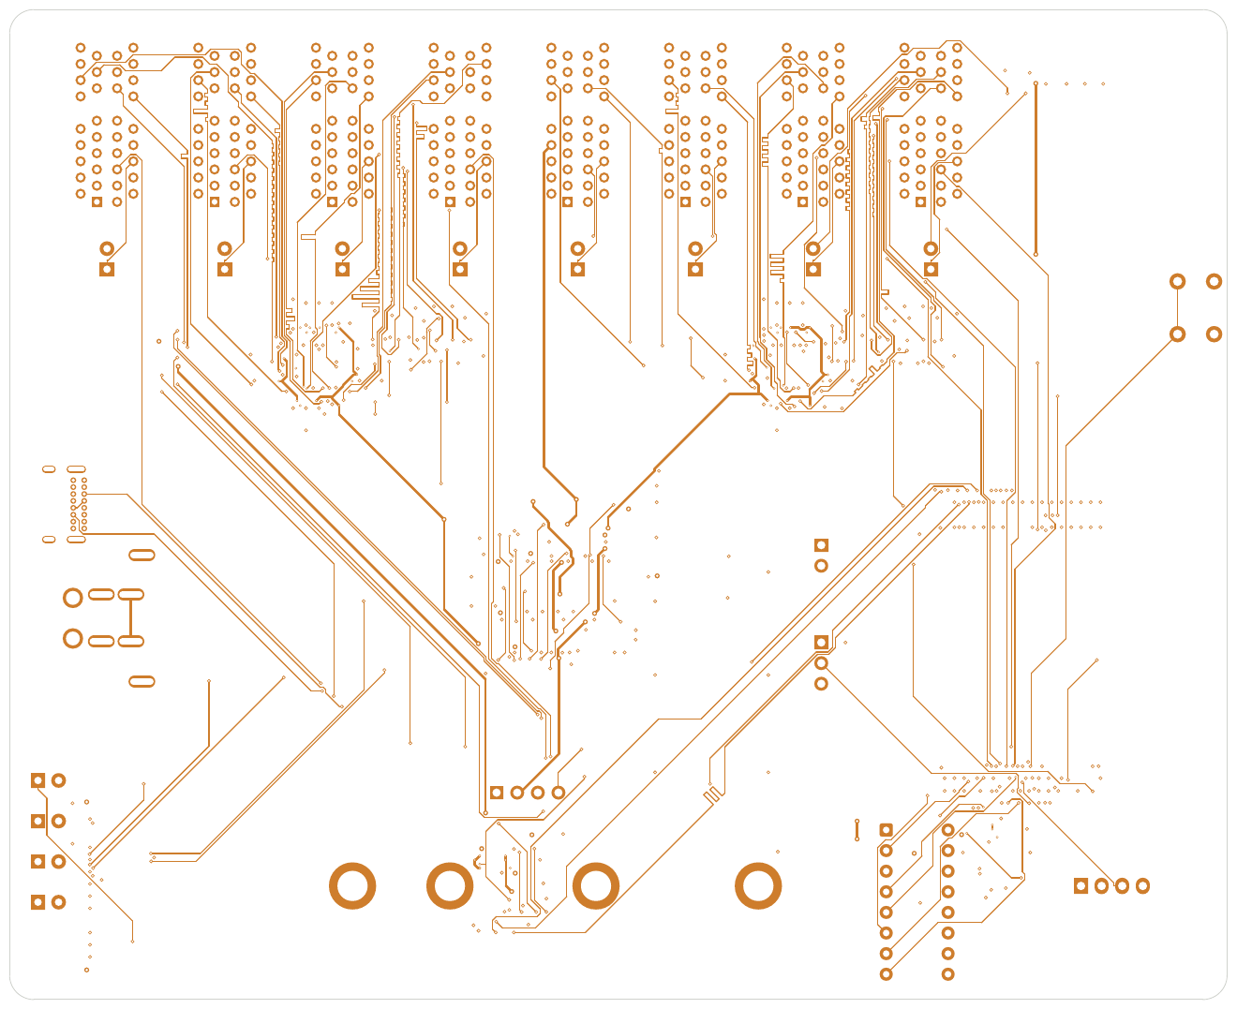
hardware/renders/layers/In2.Cu.png
