dmz006/brain-drain/hardware/renders/layers/In4.Cu.png

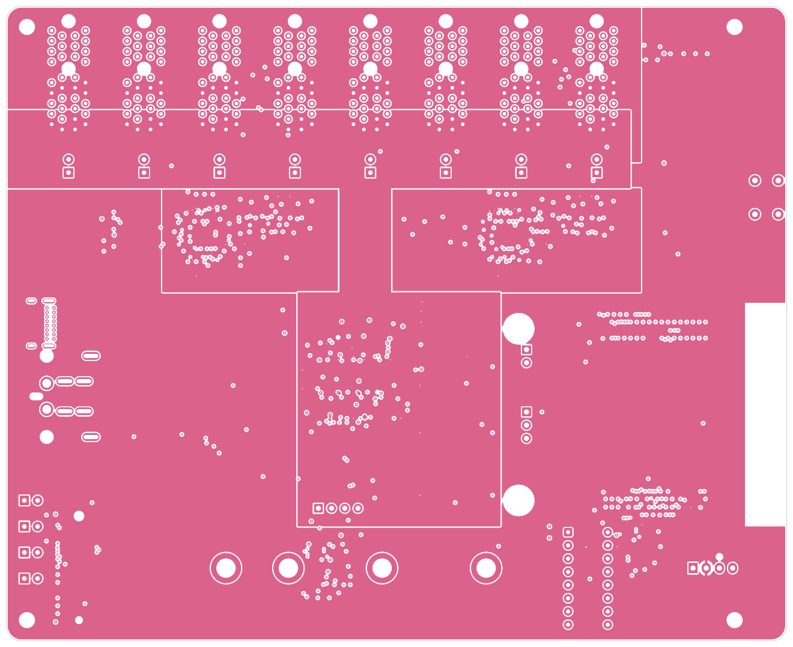
hardware/renders/layers/In4.Cu.png
