dmz006/brain-drain/hardware/renders/layers/mask.png

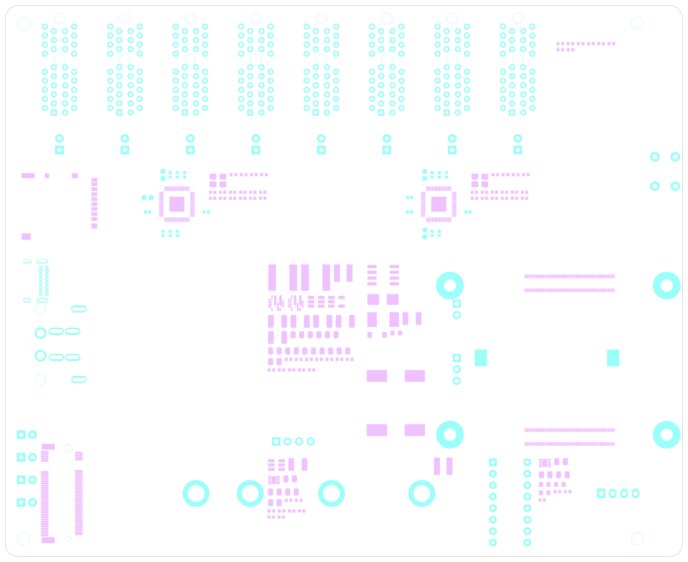
hardware/renders/layers/mask.png
