dmz006/brain-drain/hardware/renders/schematic/sheet-1.png

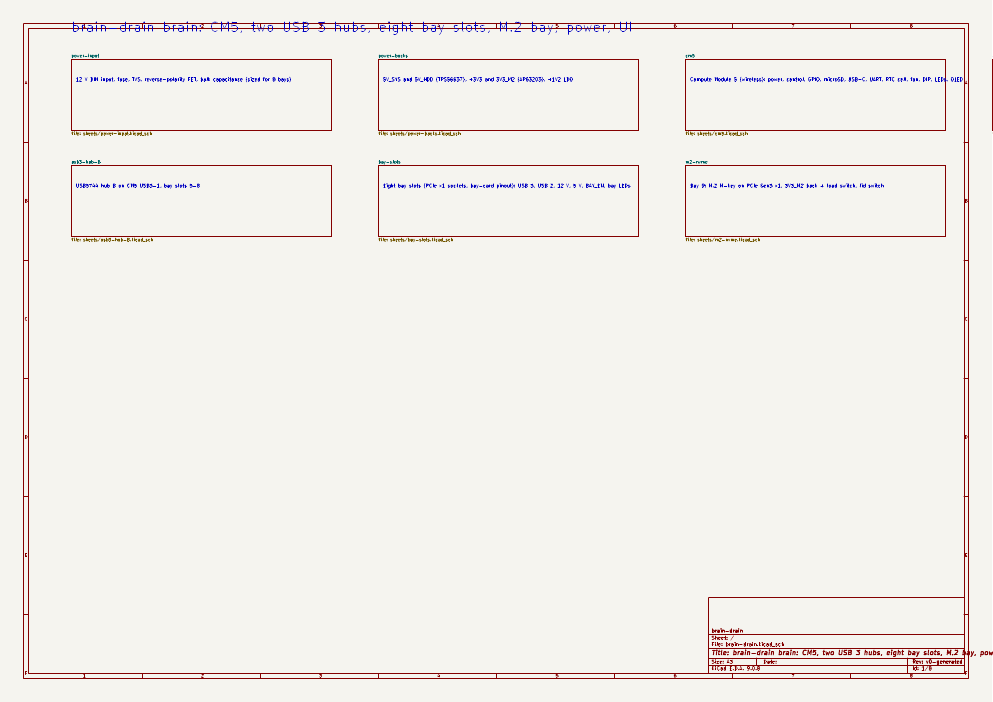
hardware/renders/schematic/sheet-1.png
