dmz006/brain-drain/hardware/renders/schematic/sheet-3.png

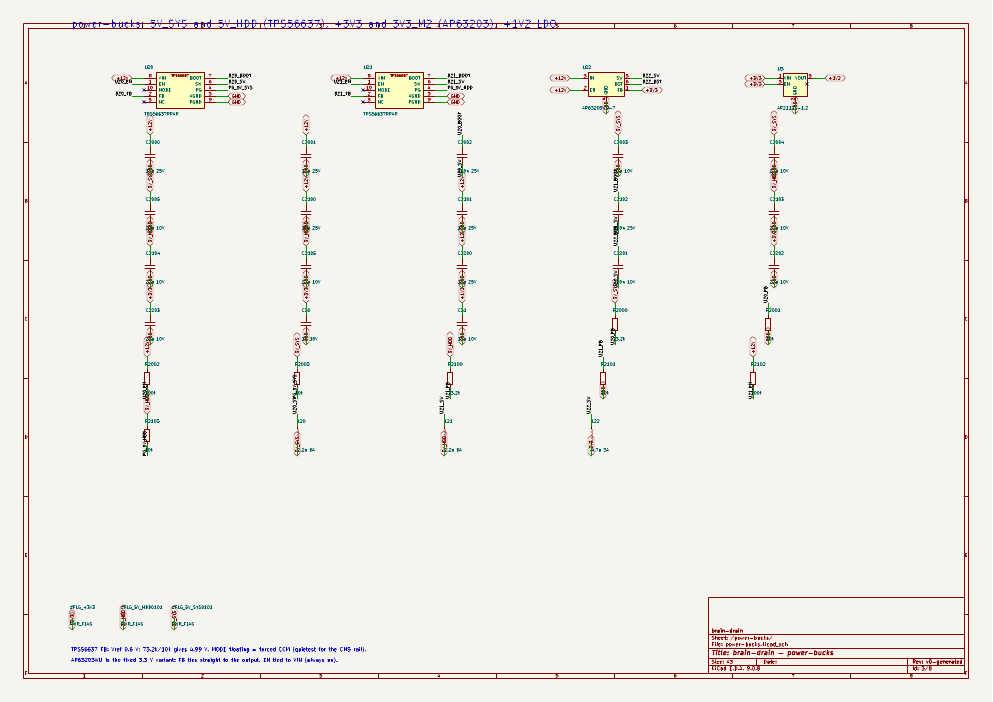
hardware/renders/schematic/sheet-3.png
