dmz006/brain-drain/hardware/renders/schematic/sheet-4.png

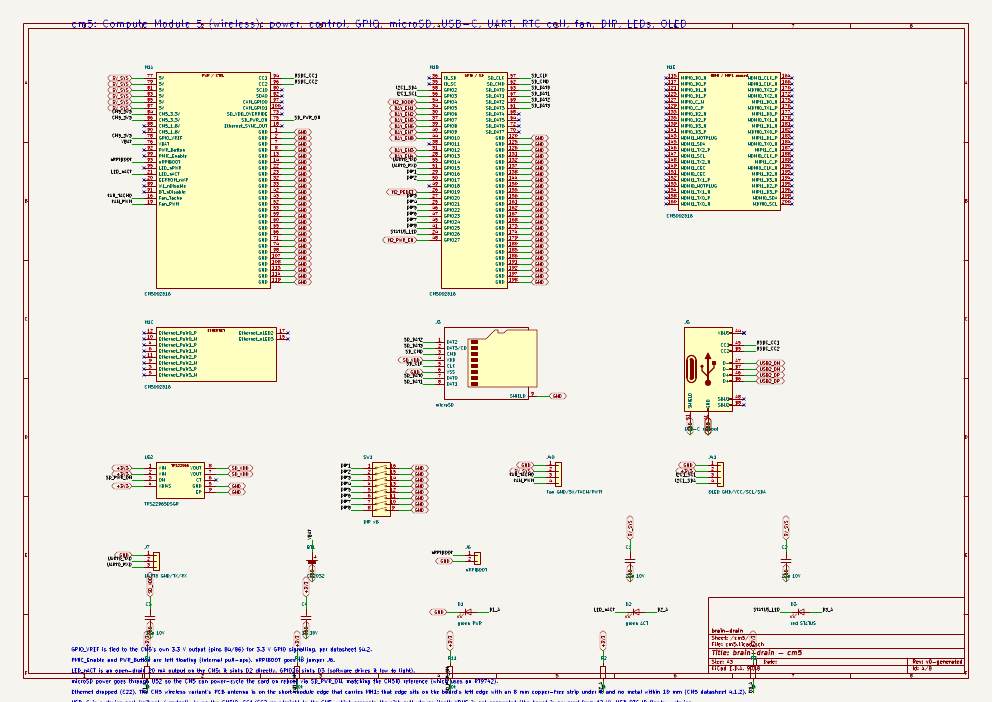
hardware/renders/schematic/sheet-4.png
