dmz006/brain-drain/hardware/renders/schematic/sheet-5.png

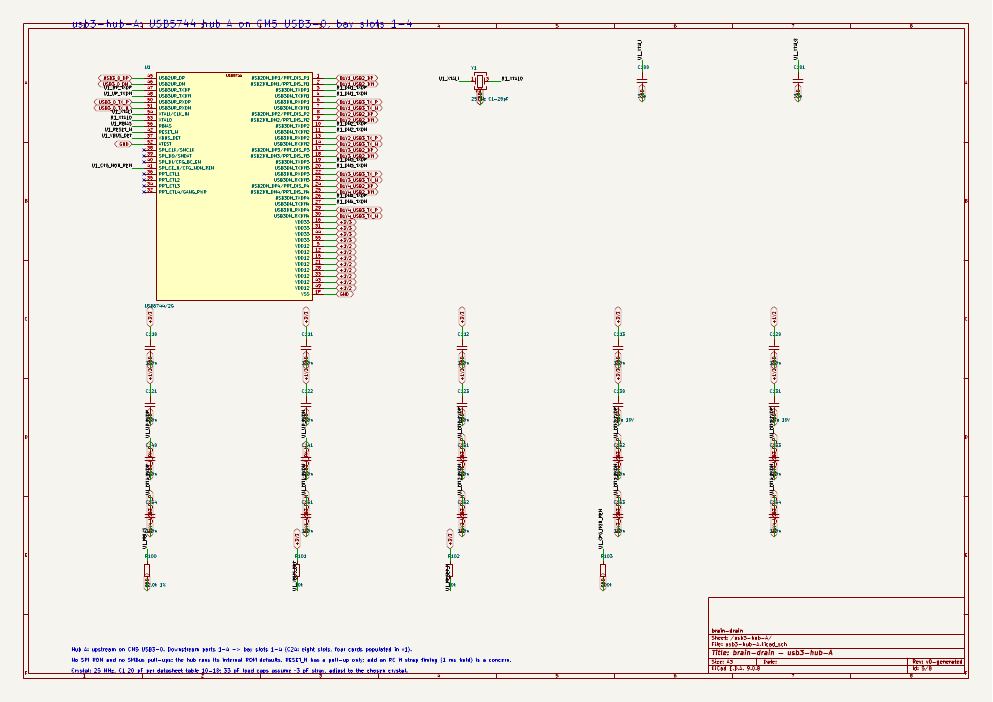
hardware/renders/schematic/sheet-5.png
