dmz006/brain-drain/hardware/renders/schematic/sheet-7.png

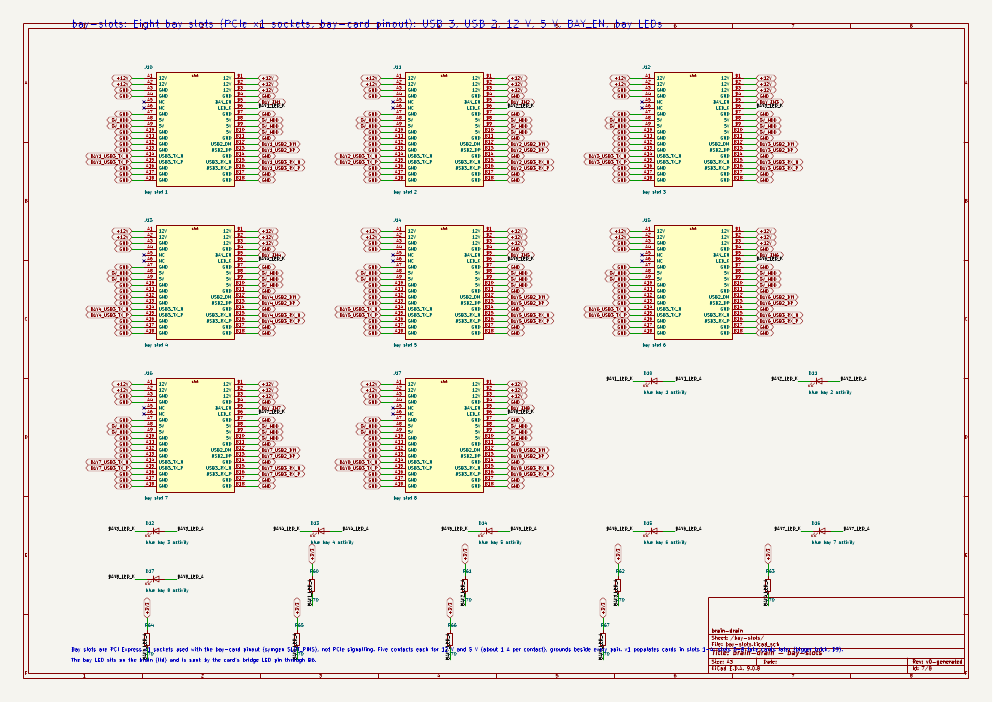
hardware/renders/schematic/sheet-7.png
