dmz006/brain-drain/hardware/renders/schematic/sheet-8.png

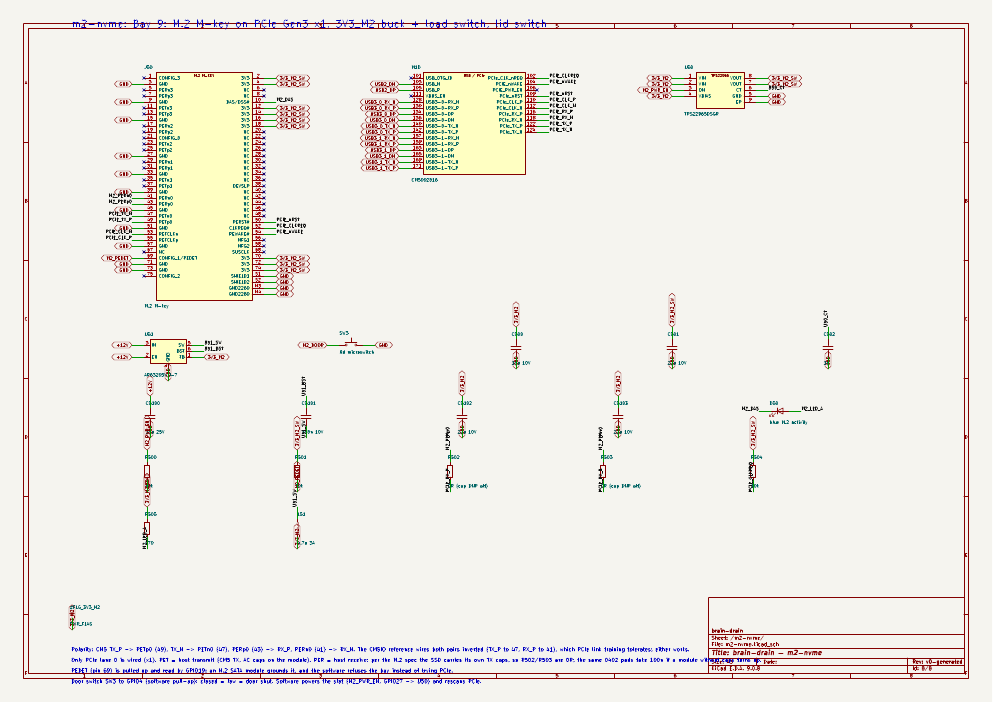
hardware/renders/schematic/sheet-8.png
