dmz006/brain-drain/hardware/bay-card/renders/layers/assembly-bottom.png

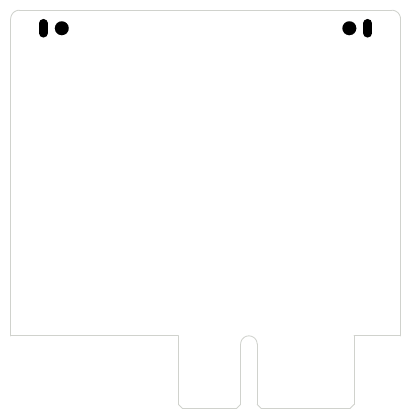
hardware/bay-card/renders/layers/assembly-bottom.png
