dmz006/brain-drain/hardware/bay-card/renders/layers/assembly-top.png

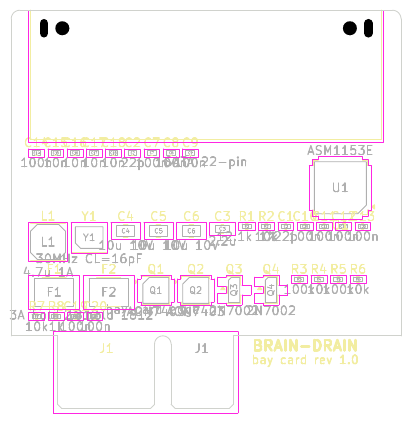
hardware/bay-card/renders/layers/assembly-top.png
