dmz006/brain-drain/hardware/renders/layers/assembly-bottom.png

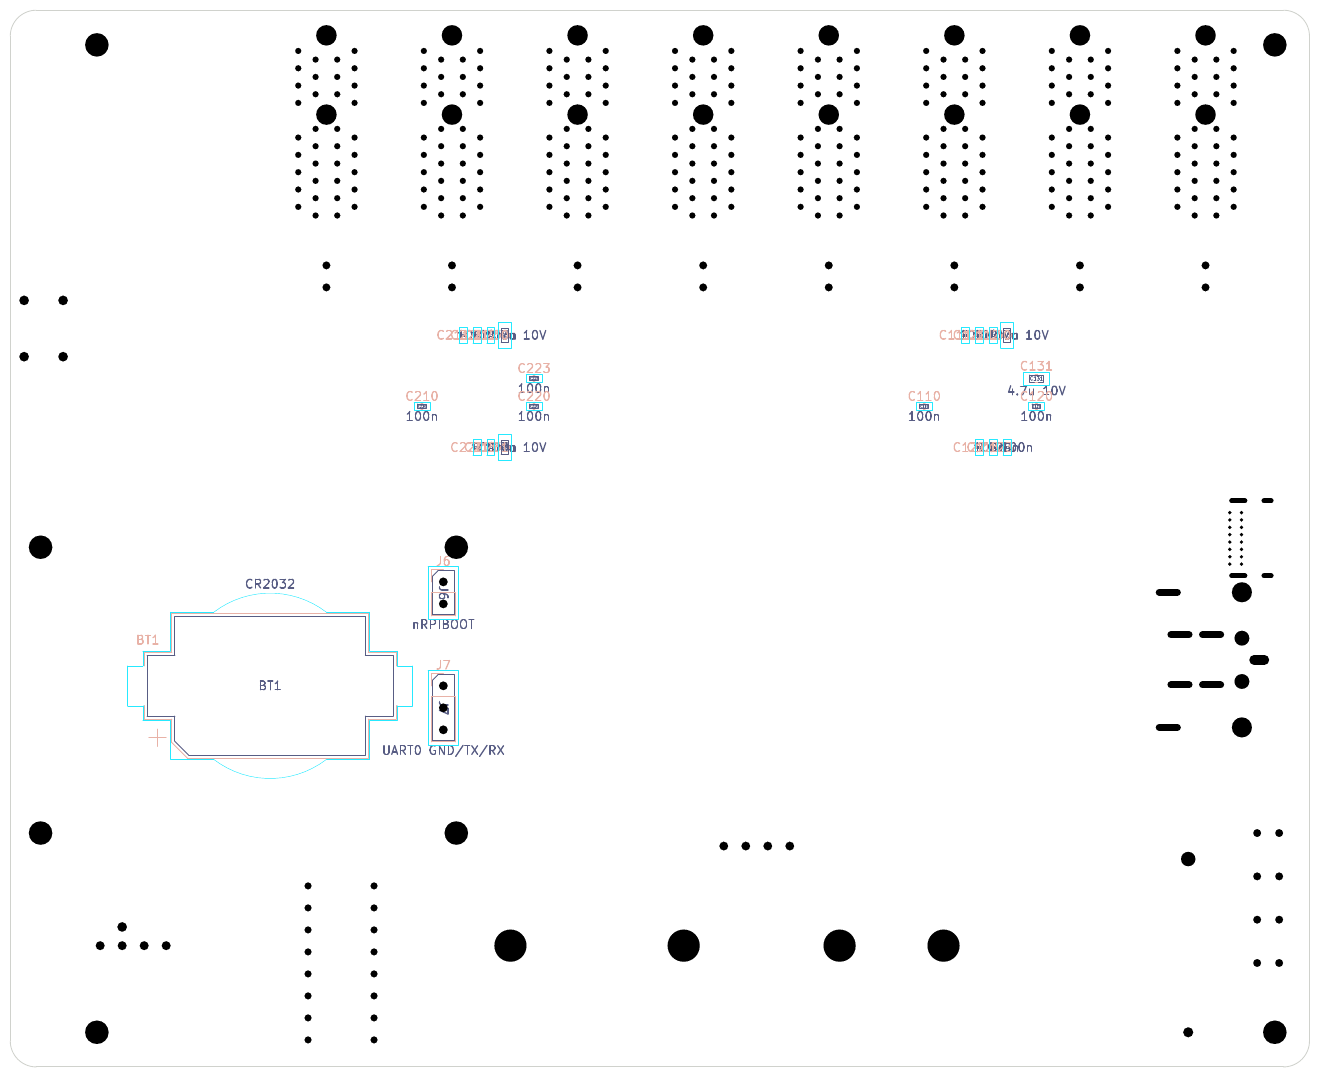
hardware/renders/layers/assembly-bottom.png
