dmz006/brain-drain/hardware/renders/layers/assembly-top.png

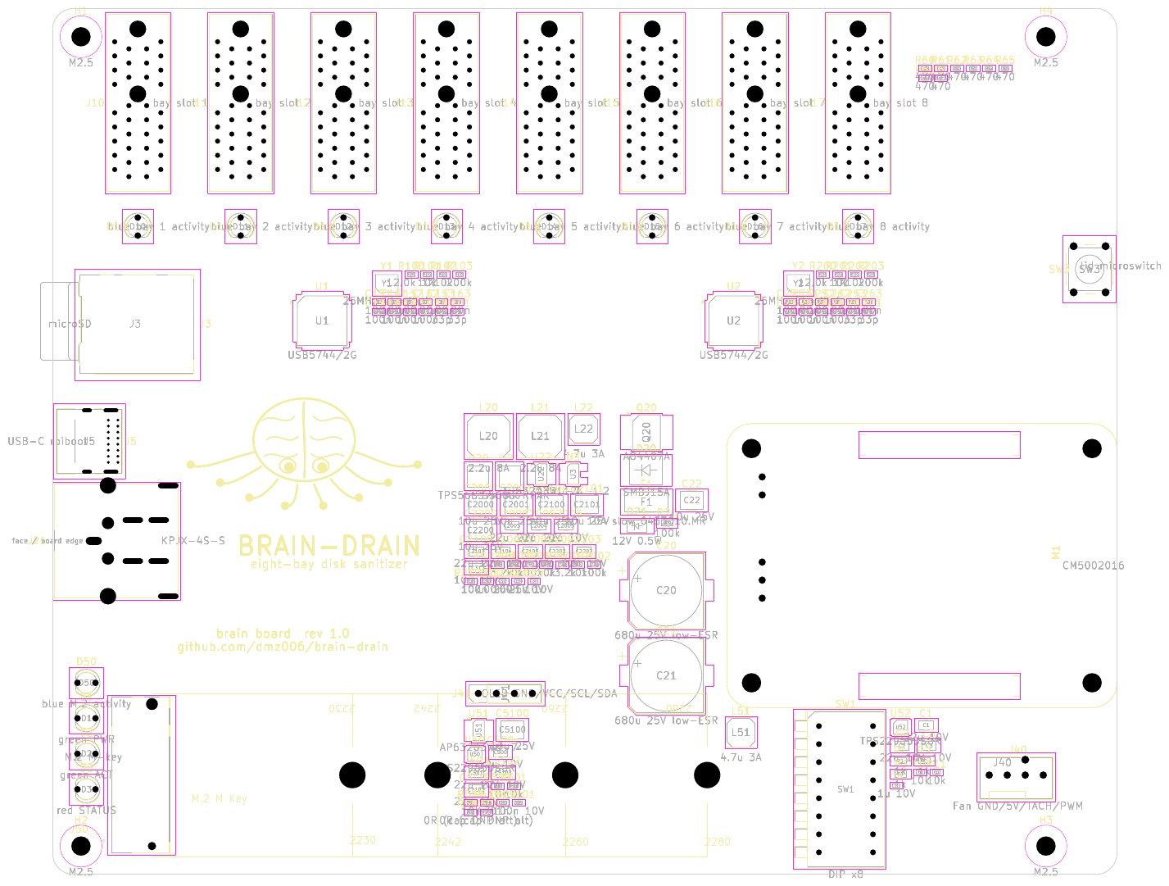
hardware/renders/layers/assembly-top.png
