dmz006/brain-drain/hardware/bay-card/routing/tune-check.png

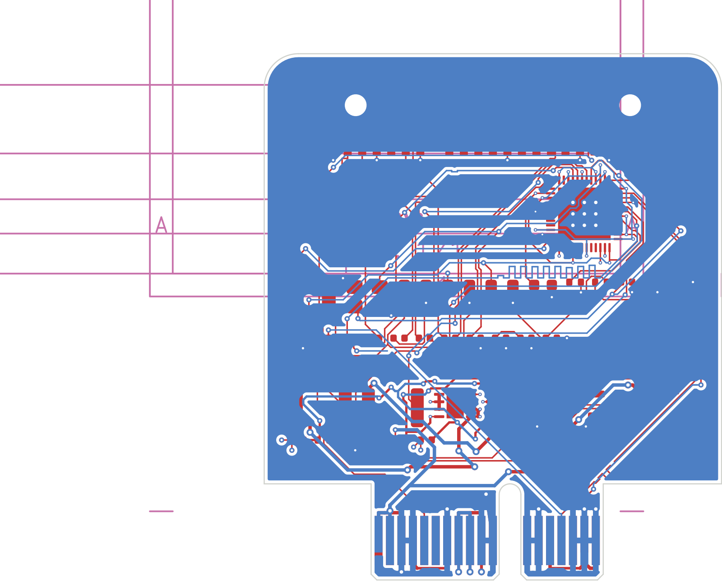
hardware/bay-card/routing/tune-check.png
