dmz006/brain-drain/enclosure/tools/kicad_to_scad.py

"""Read hardware/brain-drain.kicad_pcb and emit enclosure/board.scad.

board.scad holds the board size, the mounting holes, and every feature the
enclosure must cut or clear, in board coordinates: x from the left edge, y from
the REAR edge (the edge all cables leave through), z up from the board top.
Run from enclosure/:  python3 tools/kicad_to_scad.py
"""

from __future__ import annotations

import sys
from pathlib import Path

ROOT = Path(__file__).resolve().parents[2]
sys.path.insert(0, str(ROOT / "hardware" / "tools"))
import kifp  # noqa: E402
import sexp  # noqa: E402

PCB = ROOT / "hardware" / "brain-drain.kicad_pcb"
OUT = ROOT / "enclosure" / "board.scad"

# reference -> (kind, width, height_above_board, z_offset, note). Sizes are the
# physical part face the enclosure must clear, before clearance is added.
FEATURES = {
    # left wall (x = 0): power, rpiboot, microSD. The right wall is the CM5 antenna edge: nothing on it.
    "J21": ("left", 17.0, 16.0, 0.0, "DIN power jack face (Kycon: 16 wide, ~15 tall)"),
    "J5":  ("left", 9.5, 3.6, 0.9, "USB-C receptacle"),
    "J3":  ("left", 15.0, 3.0, 0.0, "microSD card slot"),
    # bay slots (C24): the card stands in the slot, its SATA receptacle on top pokes through a lid window
    **{f"J1{n}": ("slot", 11.8, 43.0, 0.0, f"bay slot {n + 1}: lid window for the card's 22-pin receptacle and plug") for n in range(8)},
    # under the hinged lid
    "J50": ("m2", 22.0, 80.0, 0, "M.2 socket; the SSD lies along the front under the lid, no wall slot"),
    "SW3": ("lid", 0, 0, 0, "lid microswitch (pressed by the closed lid)"),
    # lid
    "SW1": ("top", 23.0, 11.0, 0.0, "8-way DIP switch slot"),
    "J41": ("top", 30.0, 30.0, 0.0, "OLED header (module is lid-mounted on a 4-wire lead; window position in params.scad)"),
    "J40": ("top", 10.0, 5.0, 0, "fan header (optional fan)"),
    "D1":  ("led", 3.2, 0, 0, "power LED"), "D2": ("led", 3.2, 0, 0, "activity LED"), "D3": ("led", 3.2, 0, 0, "status LED"),
    **{f"D1{n}": ("led", 3.2, 0, 0, f"bay {n + 1} LED") for n in range(8)},
    "D50": ("led", 3.2, 0, 0, "M.2 LED"),
    "M1":  ("cm5", 55.0, 40.0, 0, "CM5 module centre (landscape, antenna edge at x = board_w)"),
}
SLOT_DX, SLOT_Y = 5.4, 7.2   # bay-card window offset from the slot centre, and its centre y (card: fingers at x = 6, 45 mm wide, +x to the rear)
CM5_CENTRE = (16.5, -24.0)   # module centre relative to the footprint origin (MH1) at rotation 0


def rotated(x, y, rot):
    """KiCad footprint rotation (counter-clockwise on screen, y down) applied to a local offset."""
    import math
    a = math.radians(rot)
    return x * math.cos(a) + y * math.sin(a), -x * math.sin(a) + y * math.cos(a)


def main():
    tree = sexp.parse(PCB.read_text())[0]
    # outline from Edge.Cuts lines/arcs
    xs, ys = [], []
    for tag in ("gr_line", "gr_arc"):
        for g in sexp.find_all(tree, tag):
            if str(sexp.find(g, "layer")[1]) != "Edge.Cuts":
                continue
            for pt in ("start", "end", "mid"):
                n = sexp.find(g, pt)
                if n:
                    xs.append(float(n[1])); ys.append(float(n[2]))
    ox, oy = min(xs), min(ys)
    bw, bh = max(xs) - ox, max(ys) - oy
    feats, holes = [], []
    for fp in sexp.find_all(tree, "footprint"):
        ref = next((str(p[2]) for p in sexp.find_all(fp, "property") if str(p[1]) == "Reference"), "")
        at = sexp.find(fp, "at")
        x, y = float(at[1]) - ox, float(at[2]) - oy
        rot = float(at[3]) if len(at) > 3 else 0.0
        if ref.startswith("H") and ref[1:].isdigit():
            holes.append((ref, bw - x, y))
        elif ref in FEATURES:
            kind, w, h, z, note = FEATURES[ref]
            if kind == "cm5":
                dx, dy = rotated(*CM5_CENTRE, rot)
                x, y = x + dx, y + dy
            else:   # the cutout is centred on the part's courtyard, not on the footprint origin
                bx0, by0, bx1, by1 = kifp.bbox(fp)
                corners = [rotated(cx, cy, rot) for cx, cy in ((bx0, by0), (bx1, by0), (bx1, by1), (bx0, by1))]
                x += (min(c[0] for c in corners) + max(c[0] for c in corners)) / 2
                y += (min(c[1] for c in corners) + max(c[1] for c in corners)) / 2
            if kind == "slot":
                # the window sits over the card's receptacle, not over the socket: the receptacle body (40.46 x 9.5)
                # is centred 22.5 mm from the card's edge on the card's component side, which faces +x (B contacts):
                # x + 5.4 (card face + half the 9.5 mm plug), and y = 7.2 (card front edge y 29.7 minus 22.5)
                x += SLOT_DX
                y = SLOT_Y
            # mirror x: the tray is modelled in a right-handed frame with the rear wall at y = 0, so a board that is seen
            # from the front with x to the right must be placed with x measured from the tray's x = max wall
            x = bw - x
            kind = {"left": "right", "right": "left"}.get(kind, kind)
            feats.append((ref, kind, x, y, rot, w, h, z, note))
    lines = ["// GENERATED by enclosure/tools/kicad_to_scad.py from hardware/brain-drain.kicad_pcb — do not edit",
             f"board_w = {bw:.2f};", f"board_h = {bh:.2f};",
             "// mounting holes [x, y]",
             "board_holes = [" + ", ".join(f"[{x:.2f}, {y:.2f}]" for _, x, y in holes) + "];",
             "// x is MIRRORED (measured from the board's right edge as seen from the front): the tray is right-handed with the rear wall at y = 0",
             "// features: [ref, kind, x, y, rot, w, h, z]  (x, y = part centre; kinds: left slot top led cm5 m2 lid; left/right walls are as seen from the tray frame)",
             "board_features = ["]
    for ref, kind, x, y, rot, w, h, z, note in feats:
        lines.append(f'  ["{ref}", "{kind}", {x:.2f}, {y:.2f}, {rot:.0f}, {w:.2f}, {h:.2f}, {z:.2f}],  // {note}')
    lines.append("];")
    OUT.write_text("\n".join(lines) + "\n")
    print(f"wrote {OUT.relative_to(ROOT)}: board {bw:.1f} x {bh:.1f}, {len(holes)} holes, {len(feats)} features")


if __name__ == "__main__":
    main()
